richarddzh/minibox/assets/esp32s3_devkit.jpg

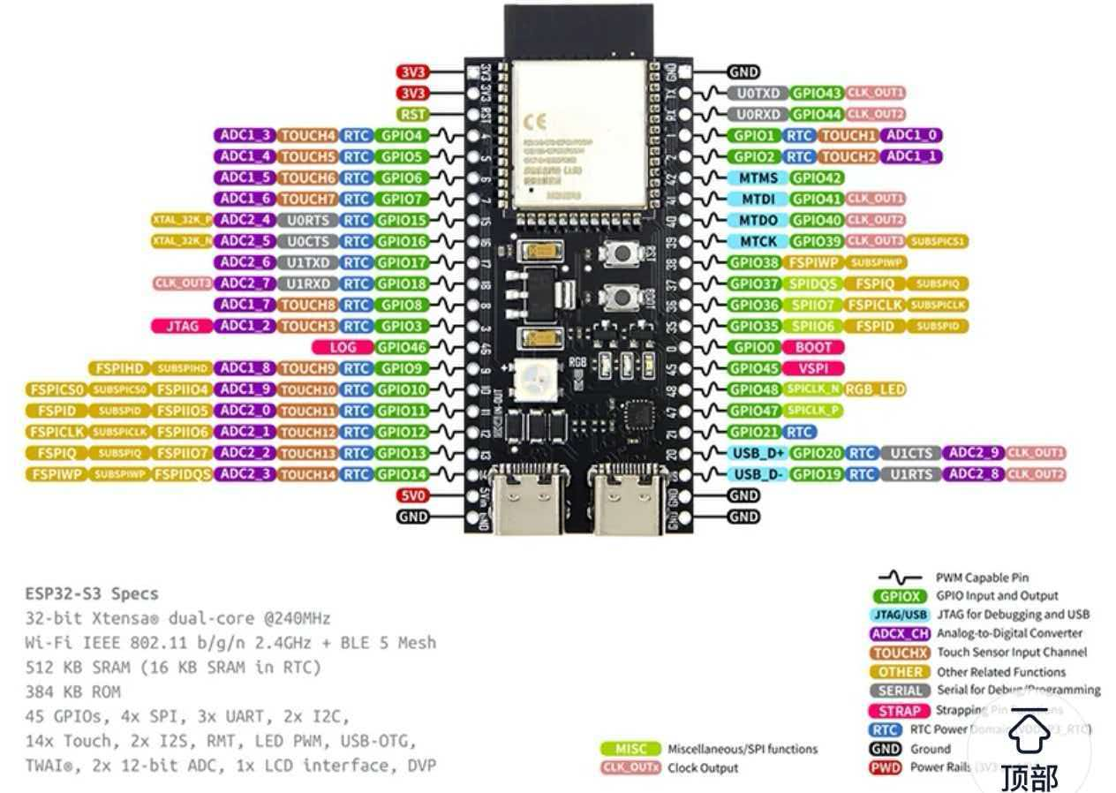
assets/esp32s3_devkit.jpg
