richarddzh/minibox/assets/keypad.jpg

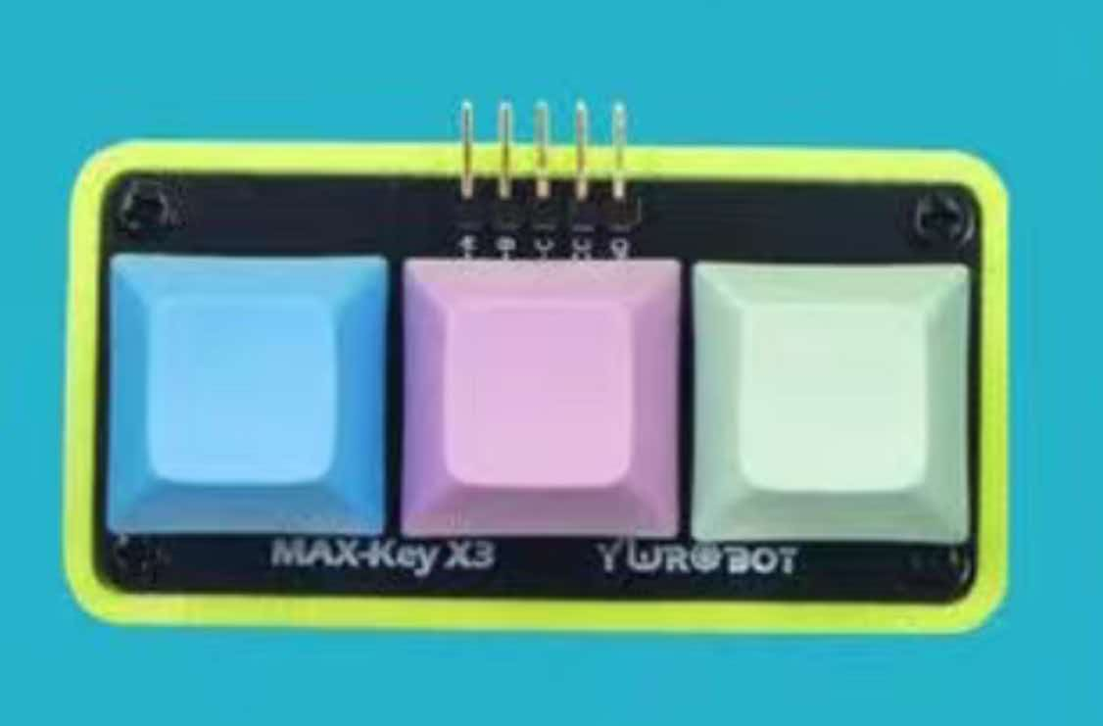
assets/keypad.jpg
