richarddzh/minibox/assets/crimp_terminal.jpg

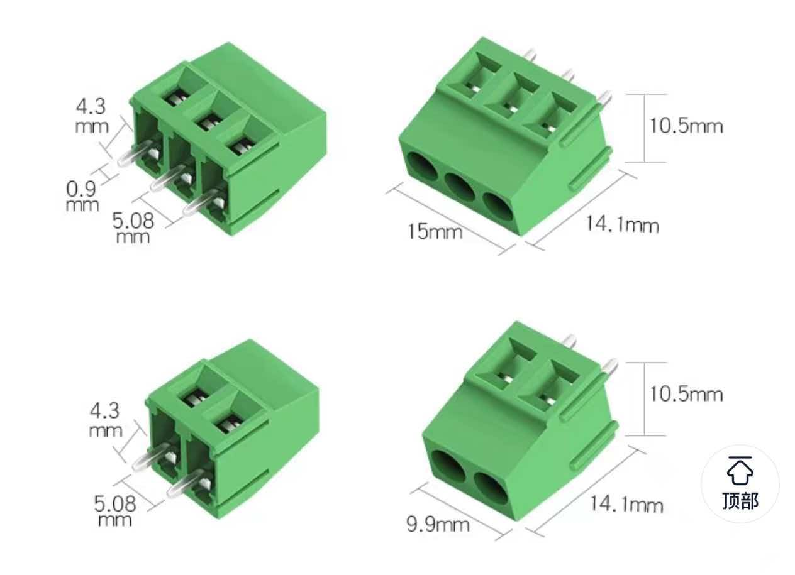
assets/crimp_terminal.jpg
