richarddzh/minibox/assets/esp32s3_devkit_01.jpg

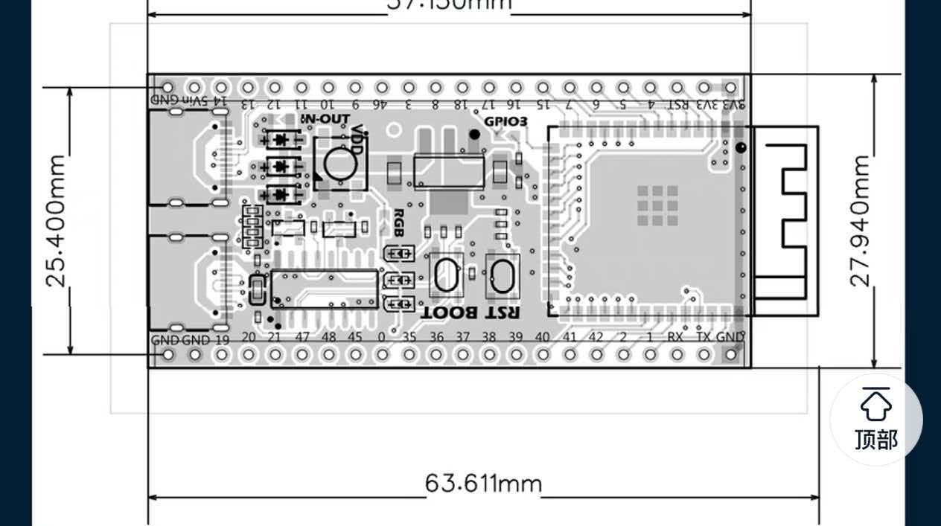
assets/esp32s3_devkit_01.jpg
