richarddzh/minibox/assets/inmp441_01.jpg

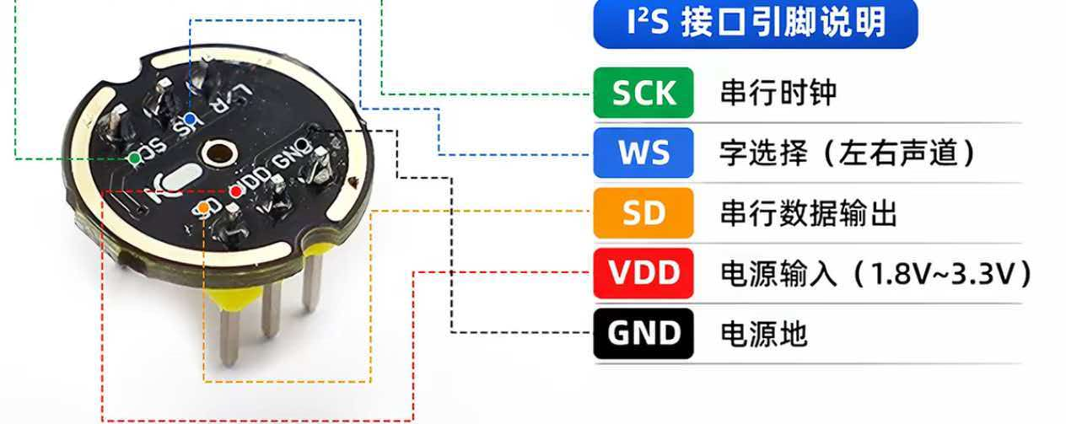
assets/inmp441_01.jpg
