richarddzh/minibox/assets/inmp441_02.jpg

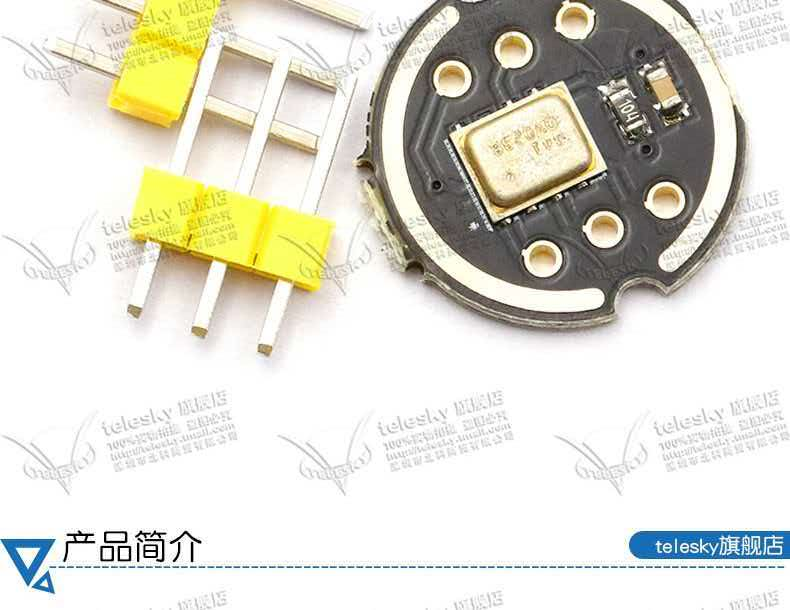
assets/inmp441_02.jpg
