richarddzh/minibox/assets/joystick.jpg

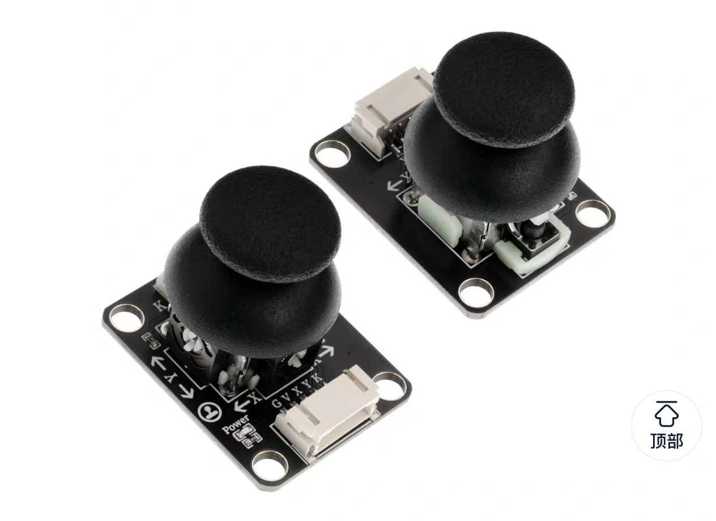
assets/joystick.jpg
