richarddzh/minibox/assets/max98357a_01.jpg

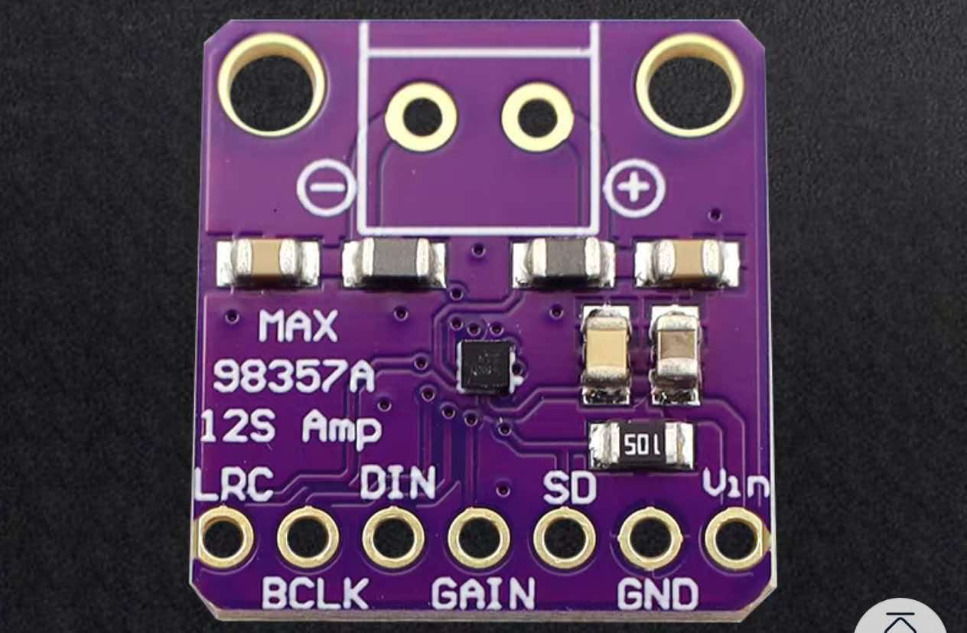
assets/max98357a_01.jpg
