richarddzh/minibox/assets/max98357a_02.jpg

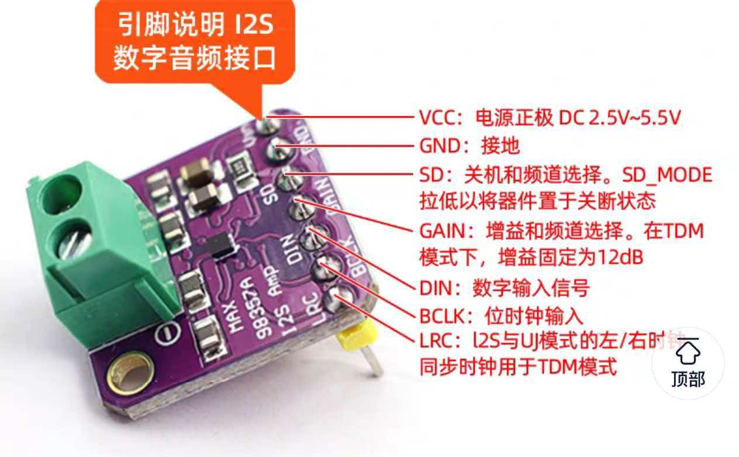
assets/max98357a_02.jpg
