richarddzh/minibox/assets/pcf8563t_rtc.jpg

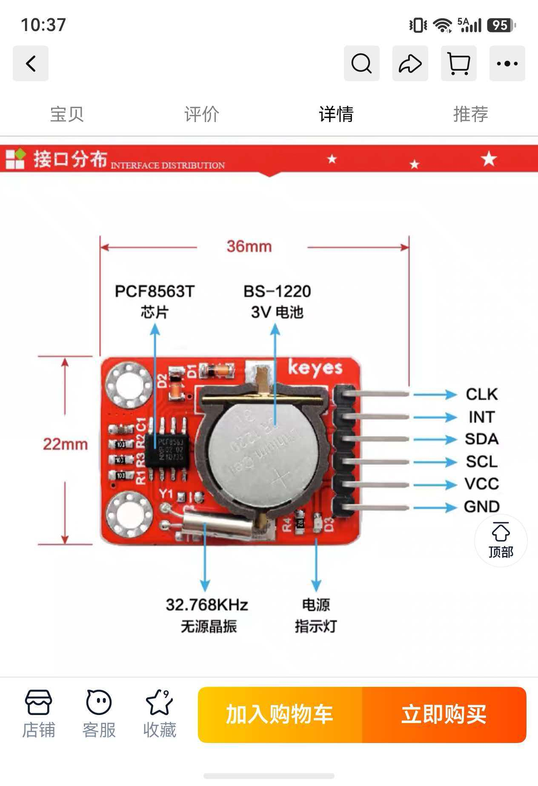
assets/pcf8563t_rtc.jpg
