richarddzh/minibox/assets/tft_spi.jpg

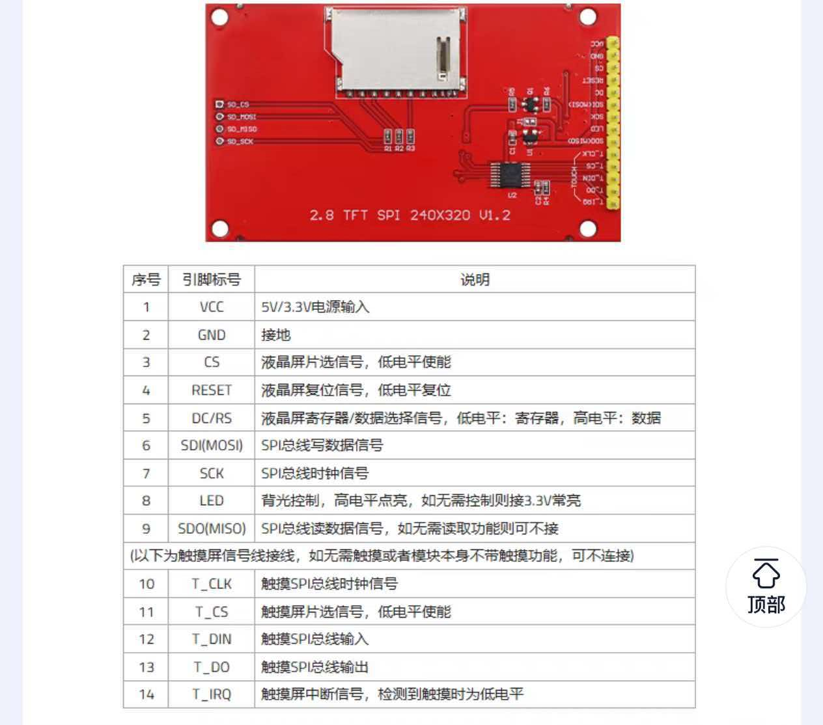
assets/tft_spi.jpg
