richarddzh/minibox/hardware_references/drawings/cpg151101d13-lcsc-pcb.png

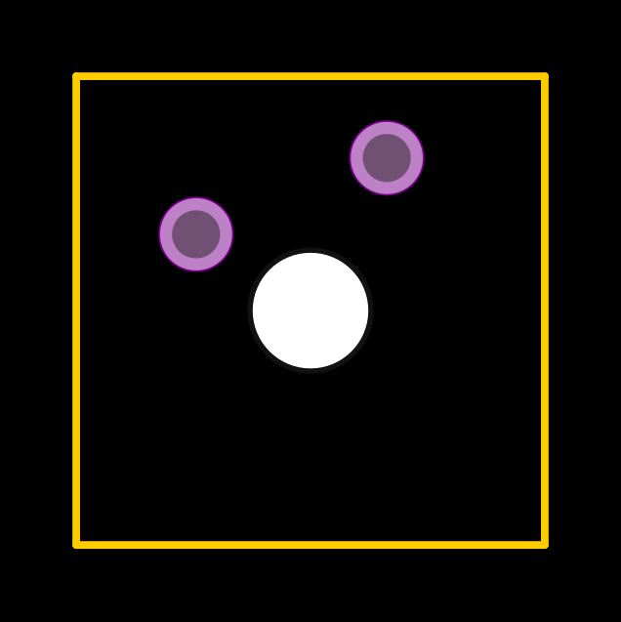
hardware_references/drawings/cpg151101d13-lcsc-pcb.png
