richarddzh/minibox/hardware_references/drawings/cpg151101d13-page-6.png

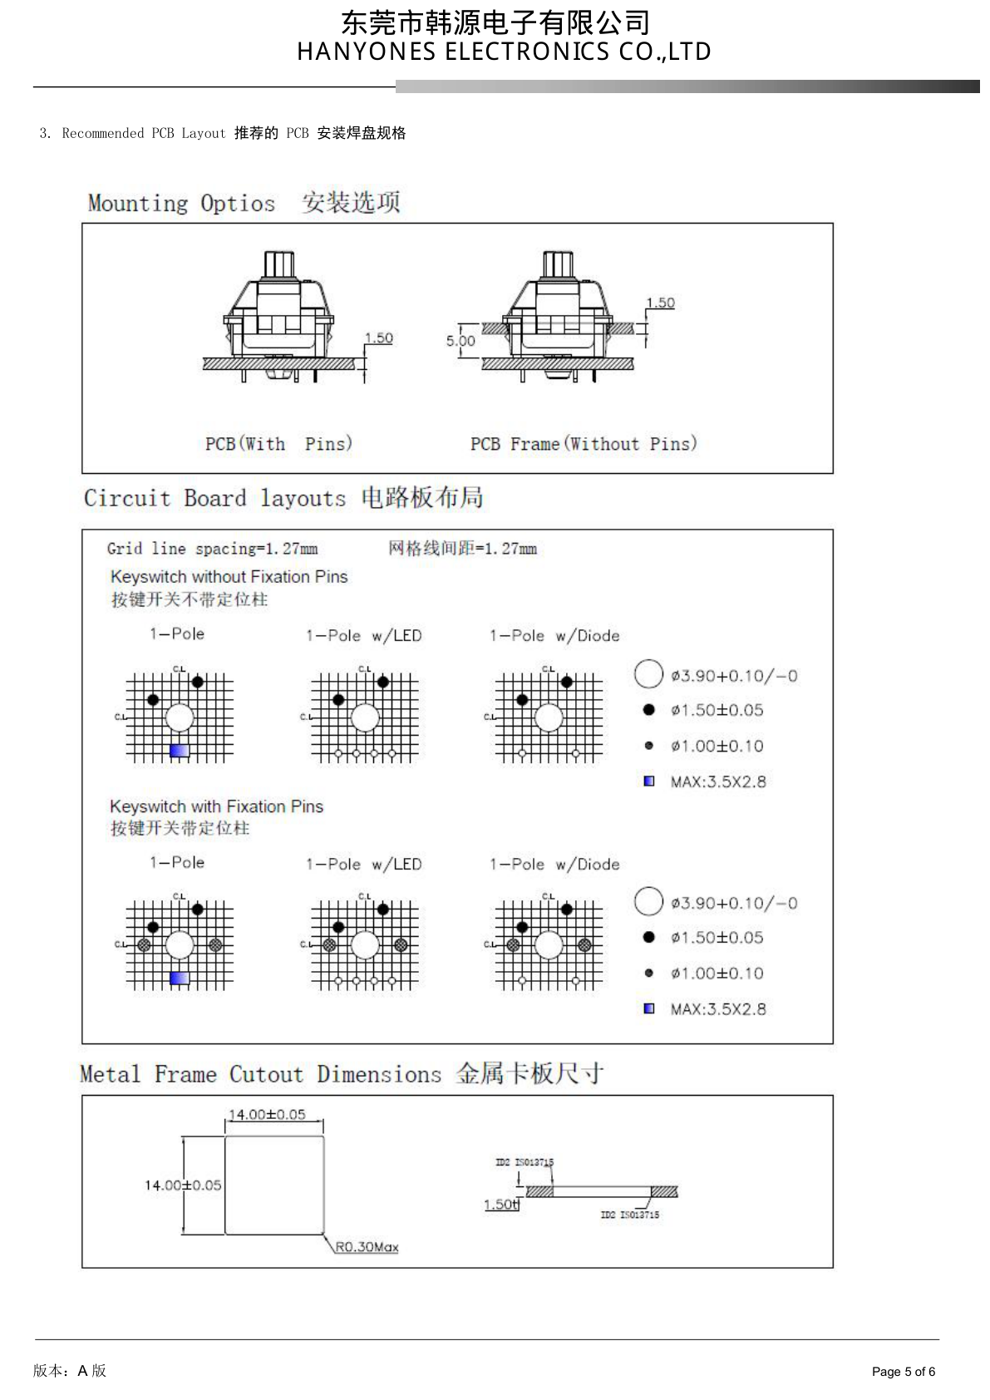
hardware_references/drawings/cpg151101d13-page-6.png
