richarddzh/minibox/hardware_references/drawings/ds3231-9.png

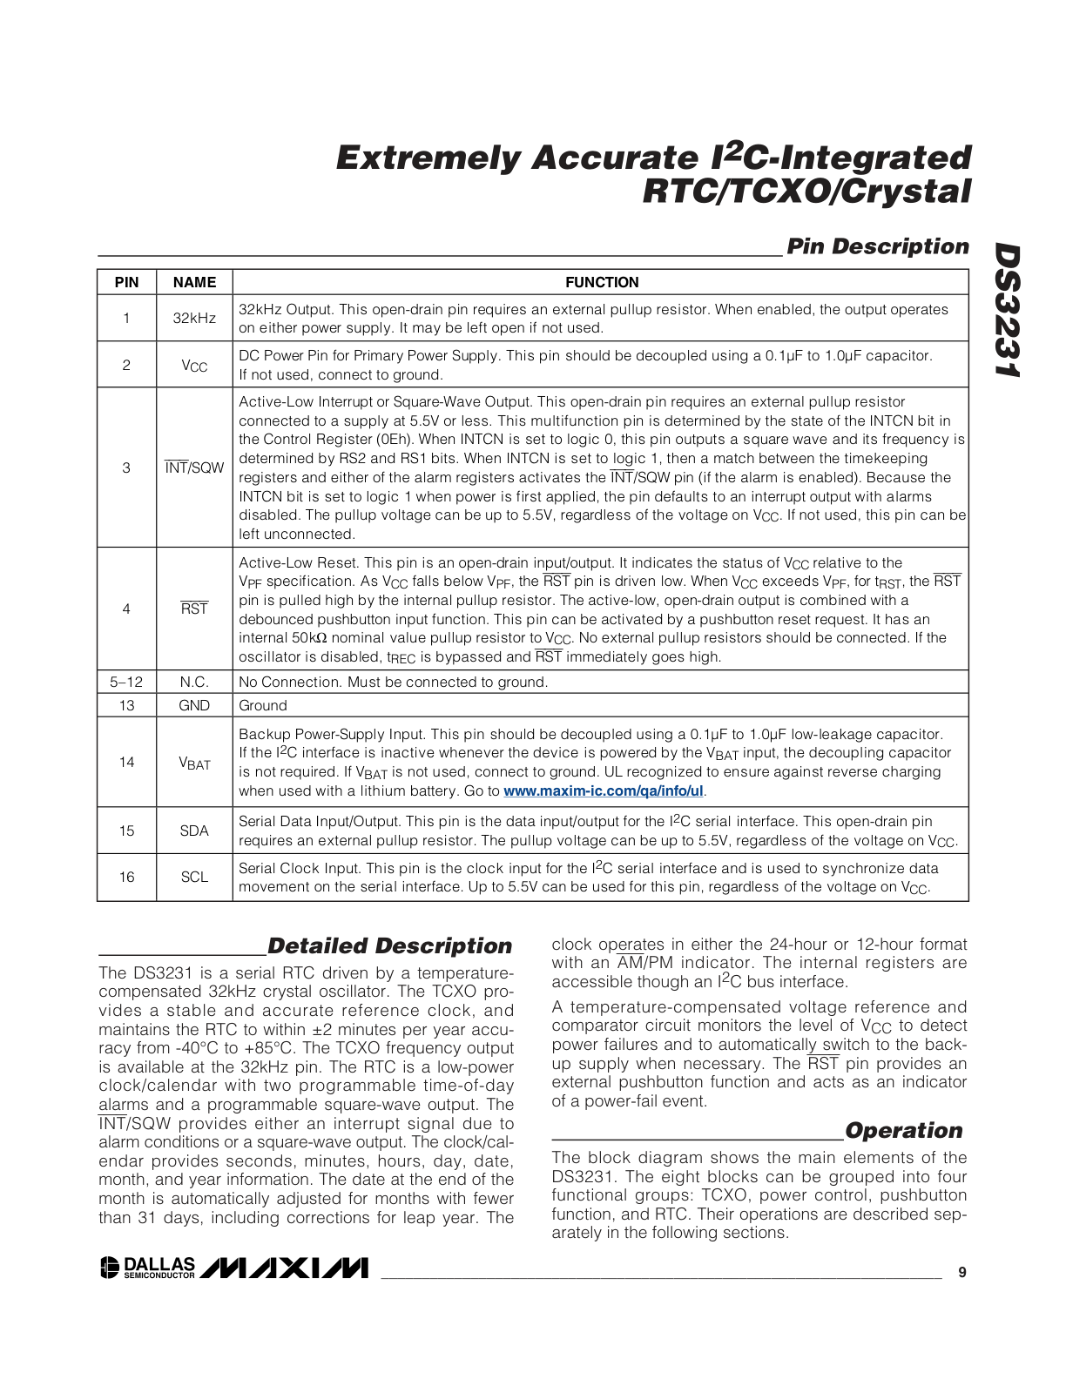
hardware_references/drawings/ds3231-9.png
