richarddzh/minibox/hardware_references/drawings/ds3231-20.png

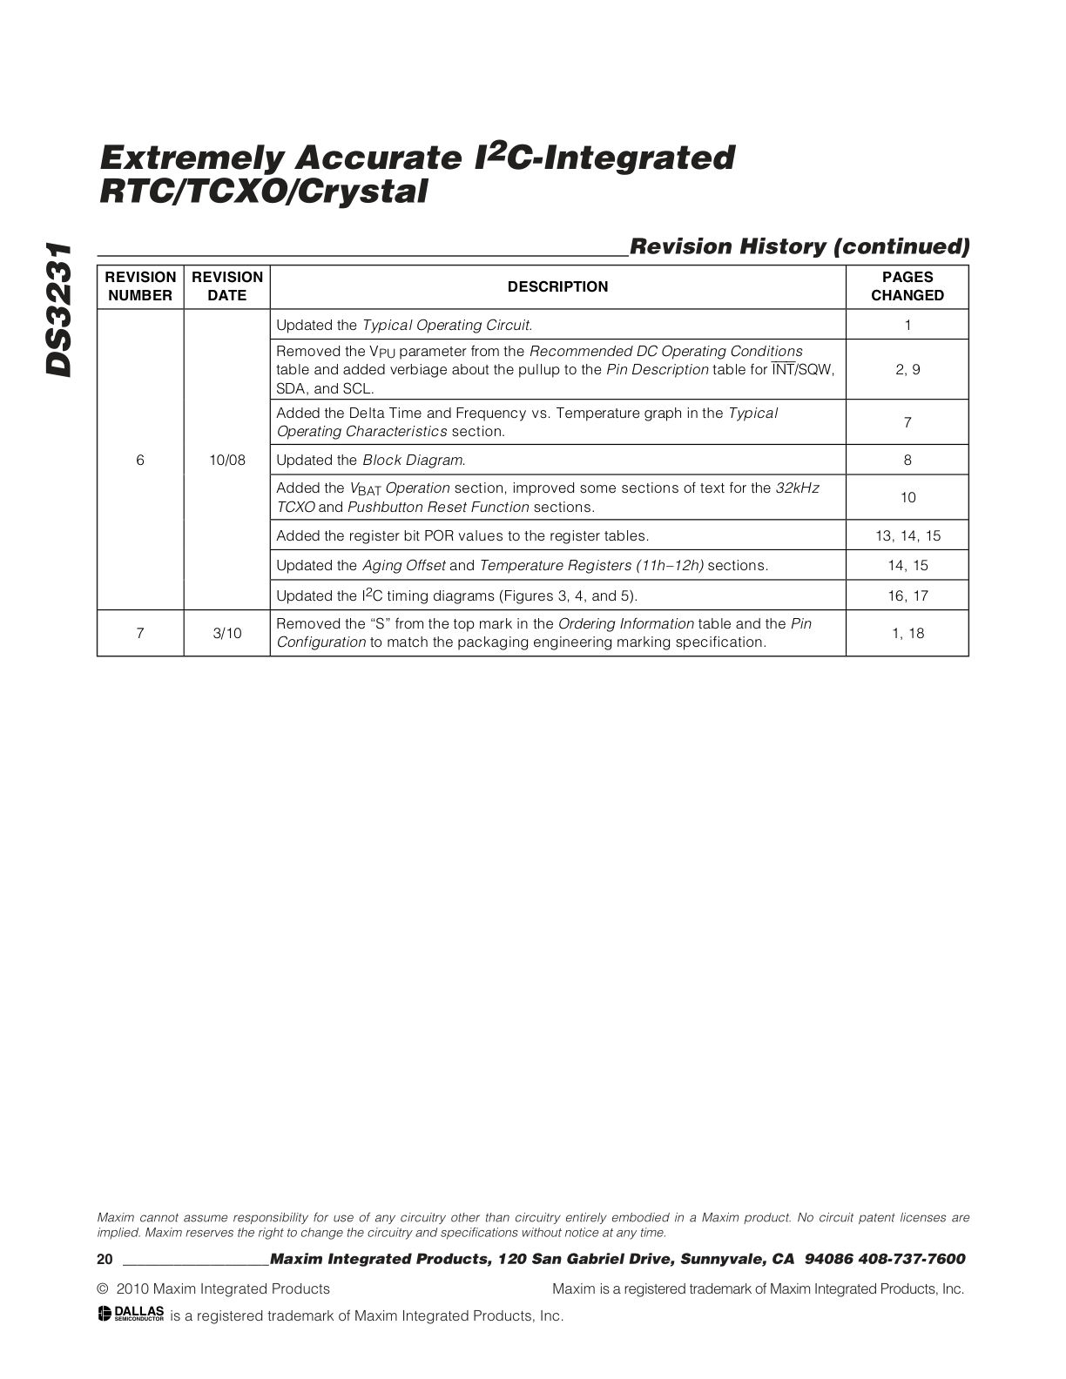
hardware_references/drawings/ds3231-20.png
