richarddzh/minibox/hardware_references/drawings/inmp441-page-8.png

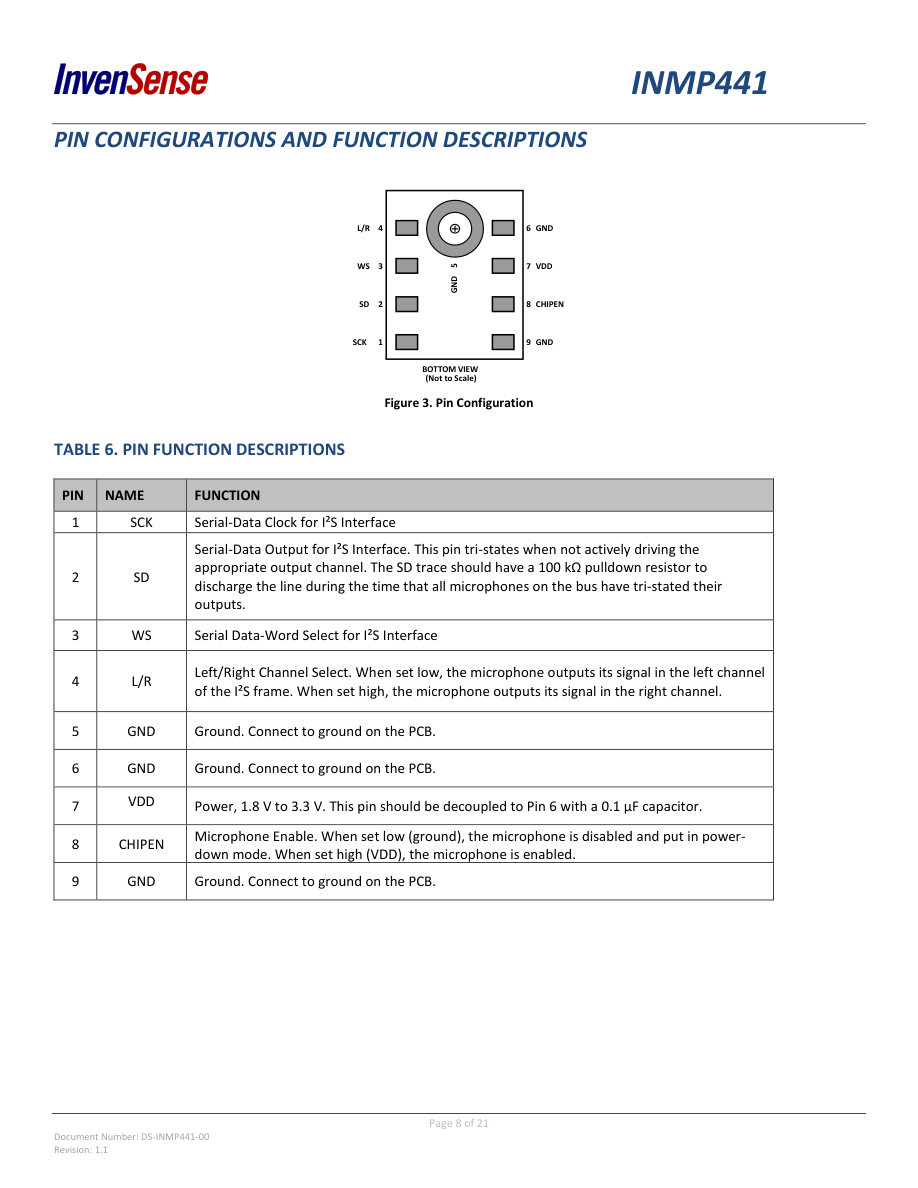
hardware_references/drawings/inmp441-page-8.png
