richarddzh/minibox/hardware_references/drawings/inmp441-page-17.png

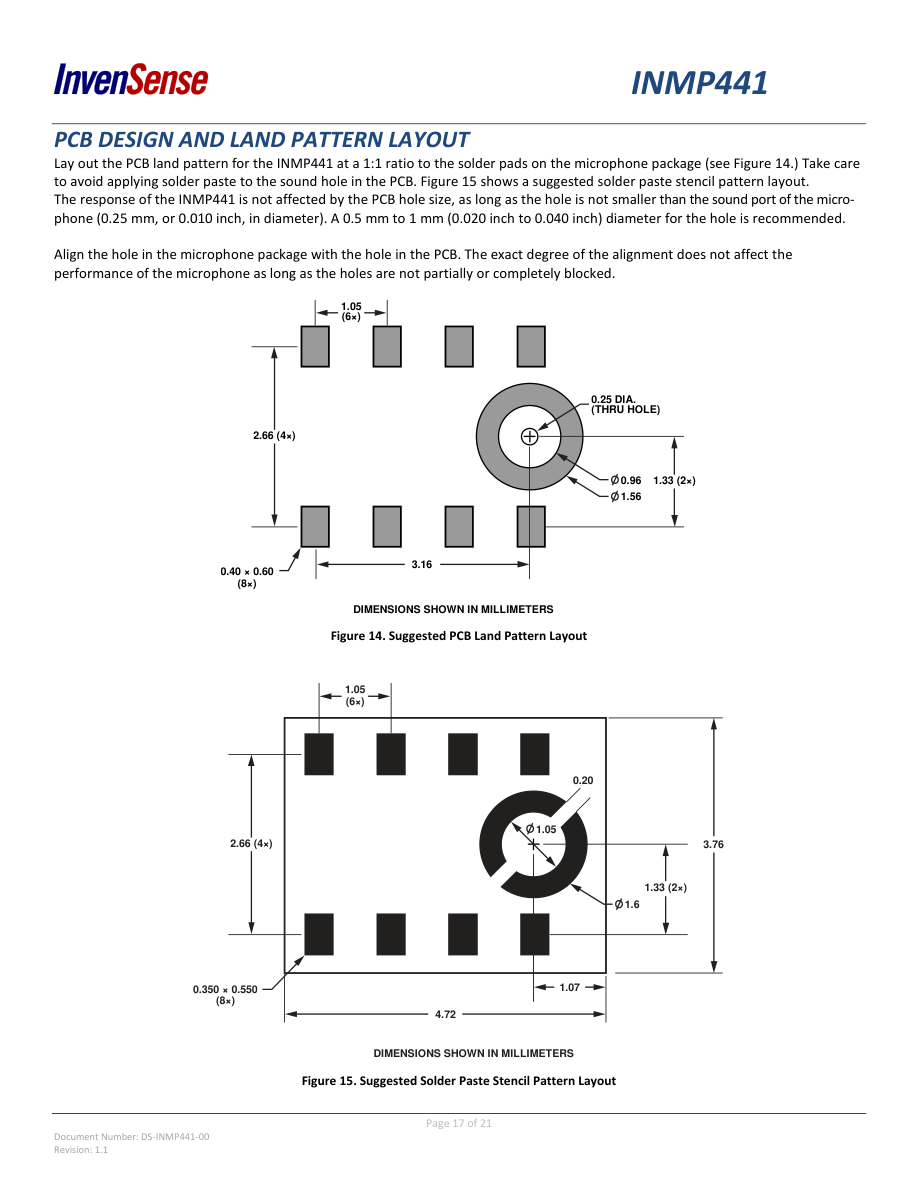
hardware_references/drawings/inmp441-page-17.png
