richarddzh/minibox/hardware_references/drawings/myoung-bs-12-b3aa003-1.png

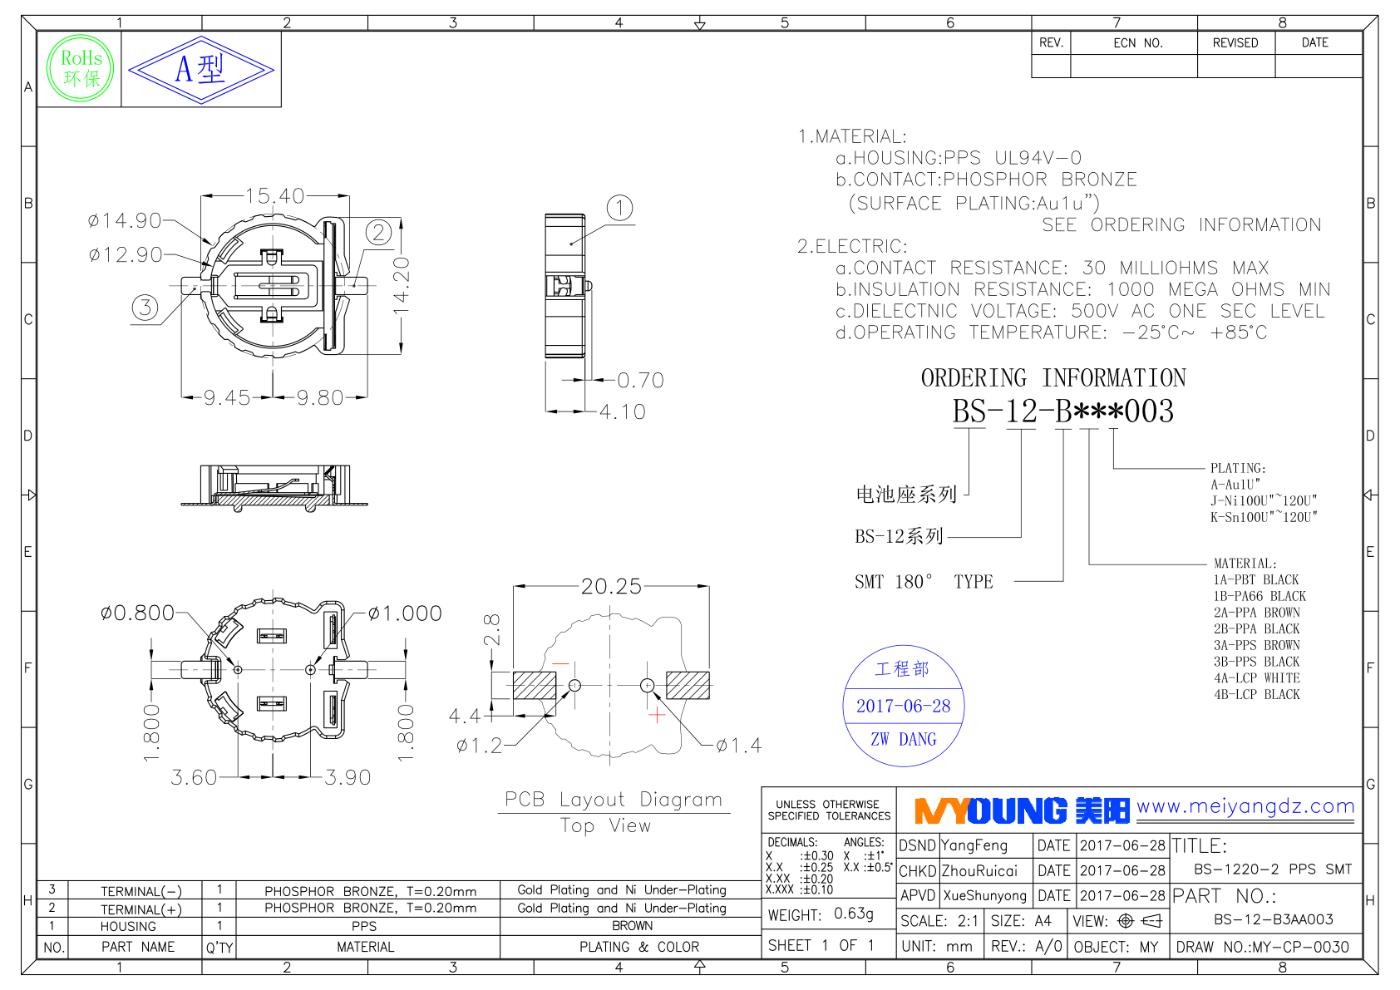
hardware_references/drawings/myoung-bs-12-b3aa003-1.png
