richarddzh/minibox/hardware_references/drawings/requested-layout-20261009.png

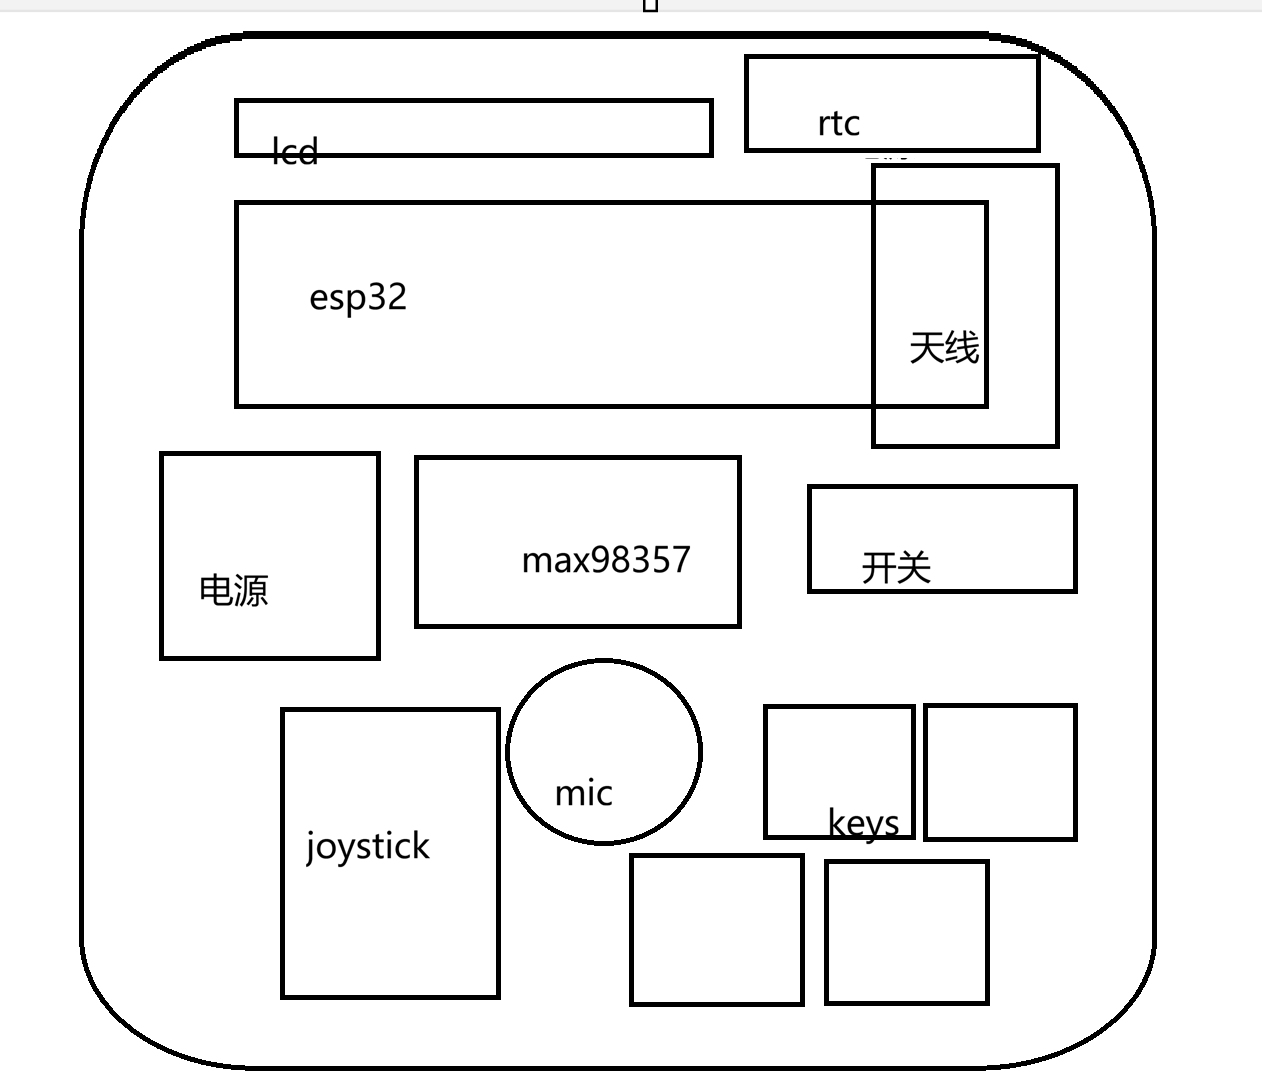
hardware_references/drawings/requested-layout-20261009.png
