richarddzh/minibox/hardware_references/drawings/requested-layout.png

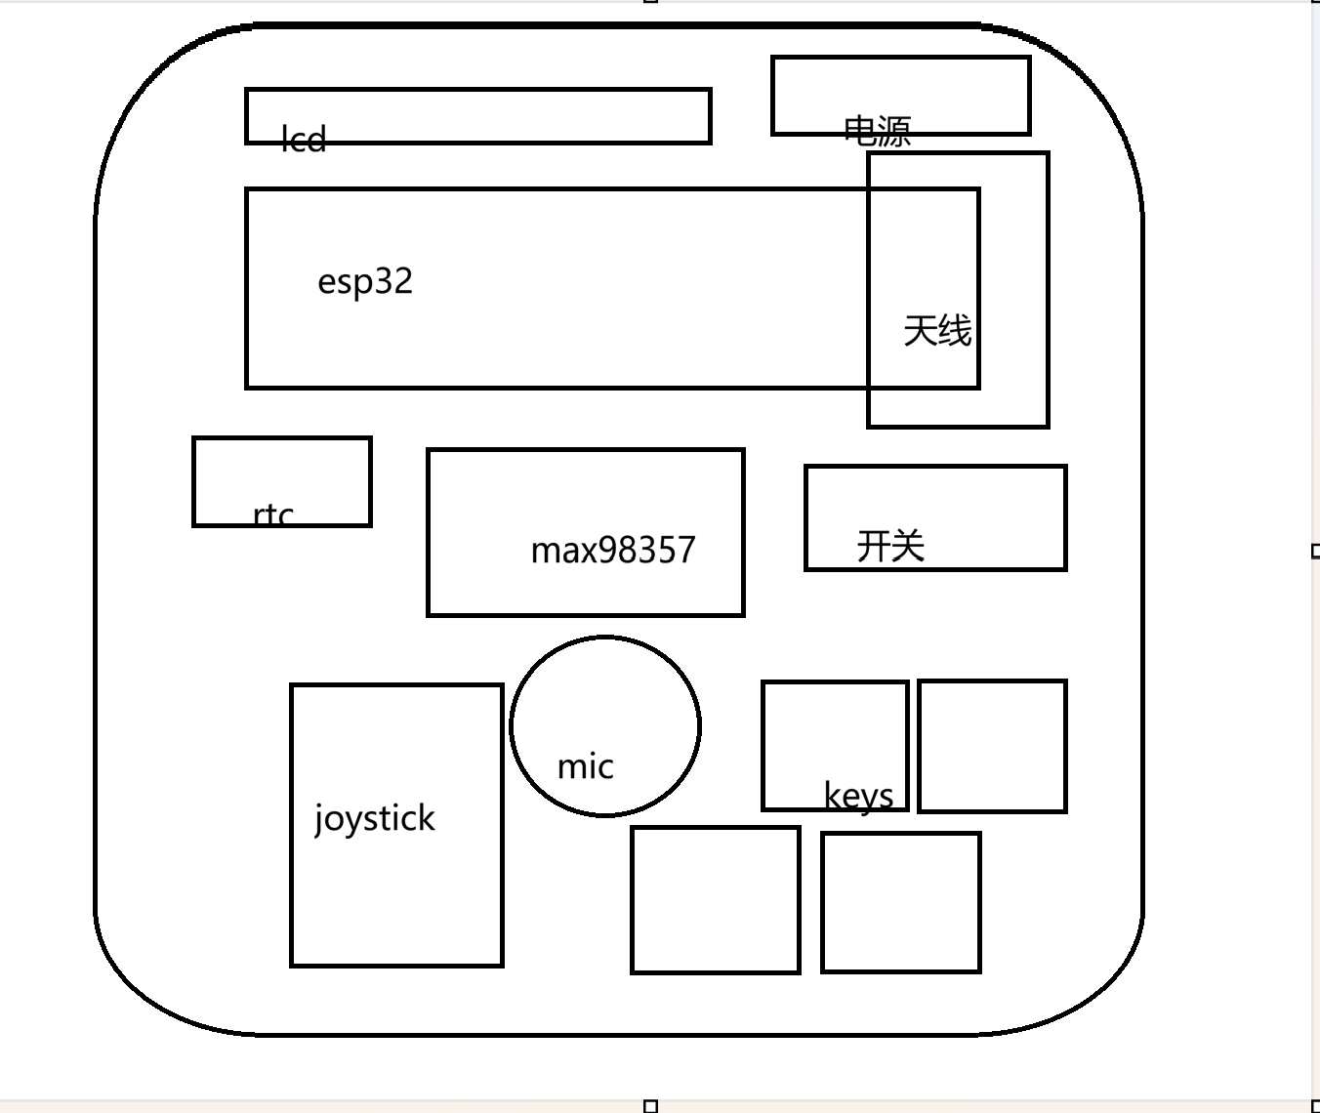
hardware_references/drawings/requested-layout.png
