richarddzh/minibox/hardware_references/drawings/rkjxv-2.png

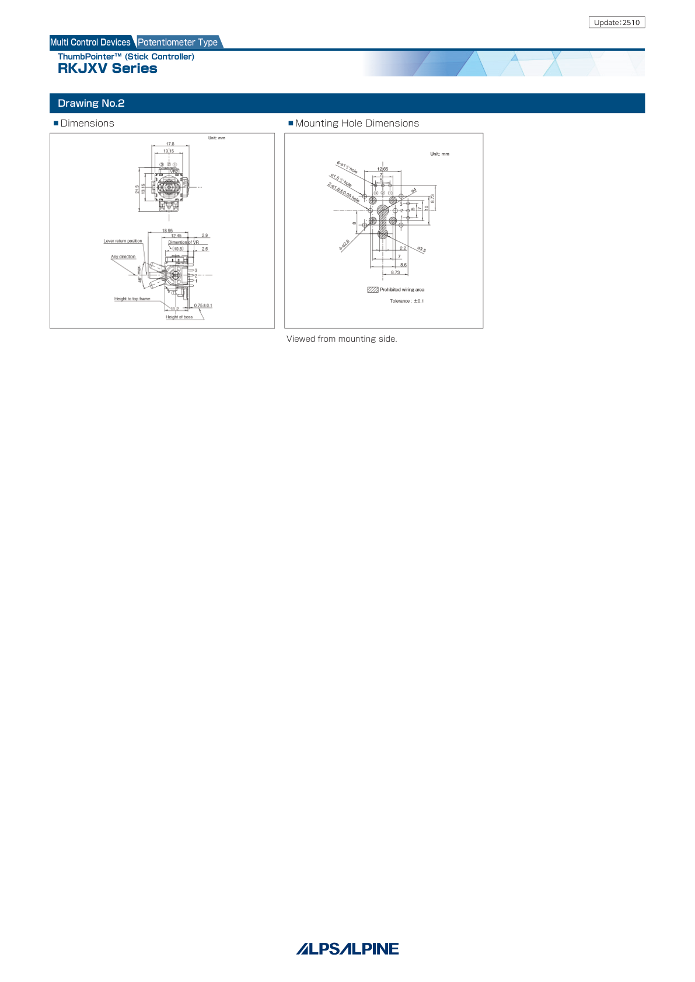
hardware_references/drawings/rkjxv-2.png
