richarddzh/minibox/hardware_references/drawings/sn74lvc1g11-pins-3.png

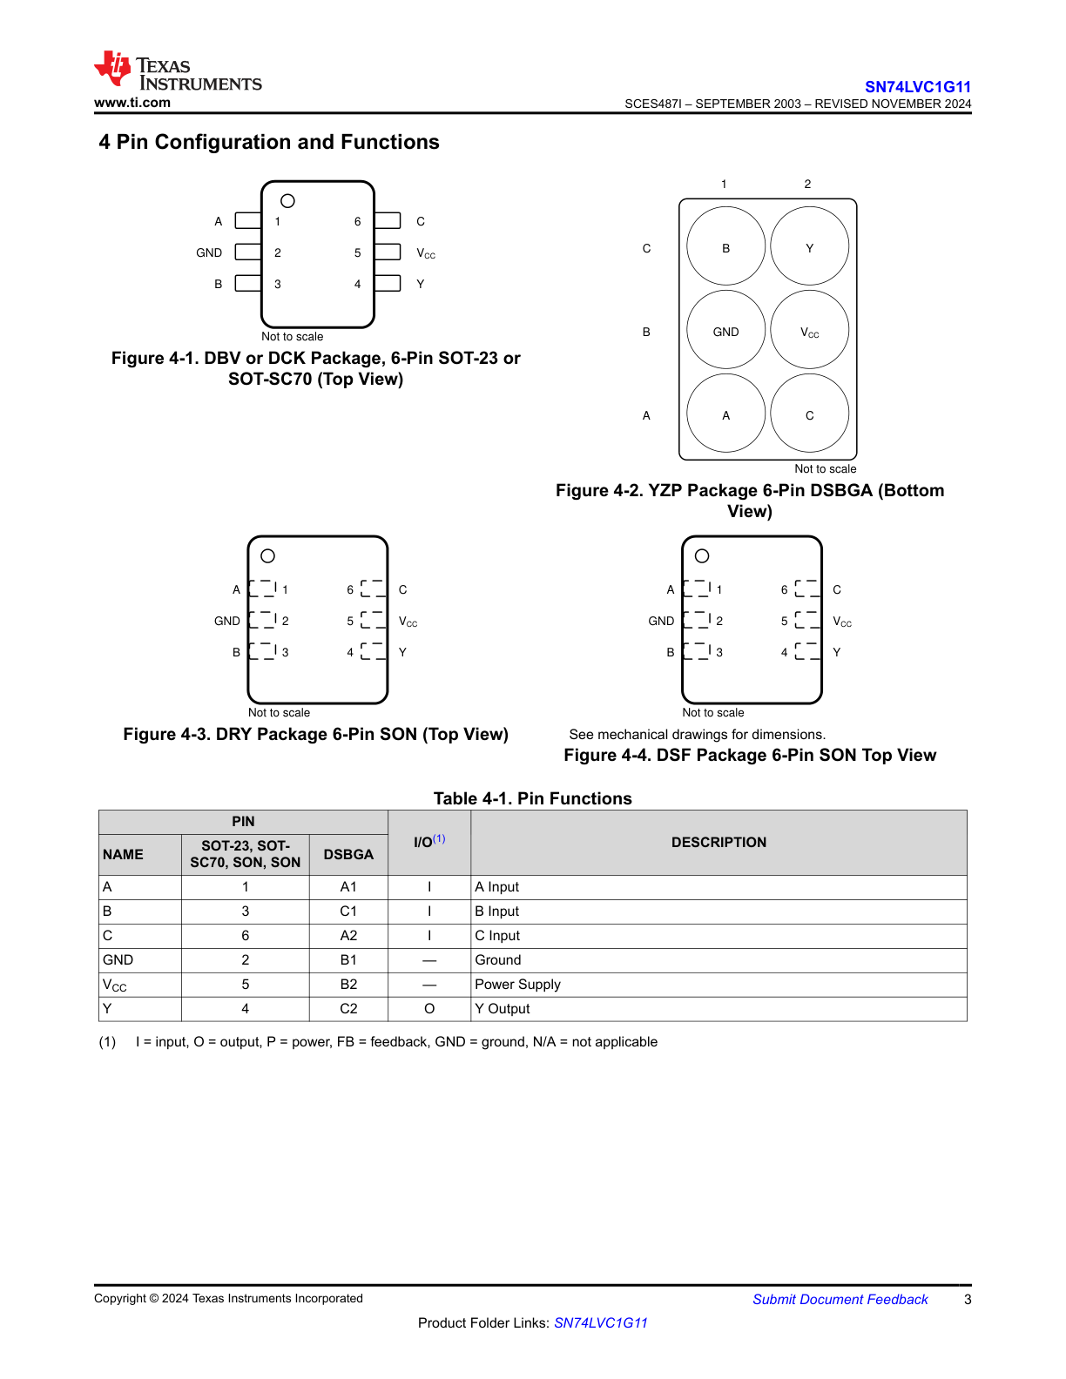
hardware_references/drawings/sn74lvc1g11-pins-3.png
