richarddzh/minibox/hardware_references/drawings/thb001p-1.png

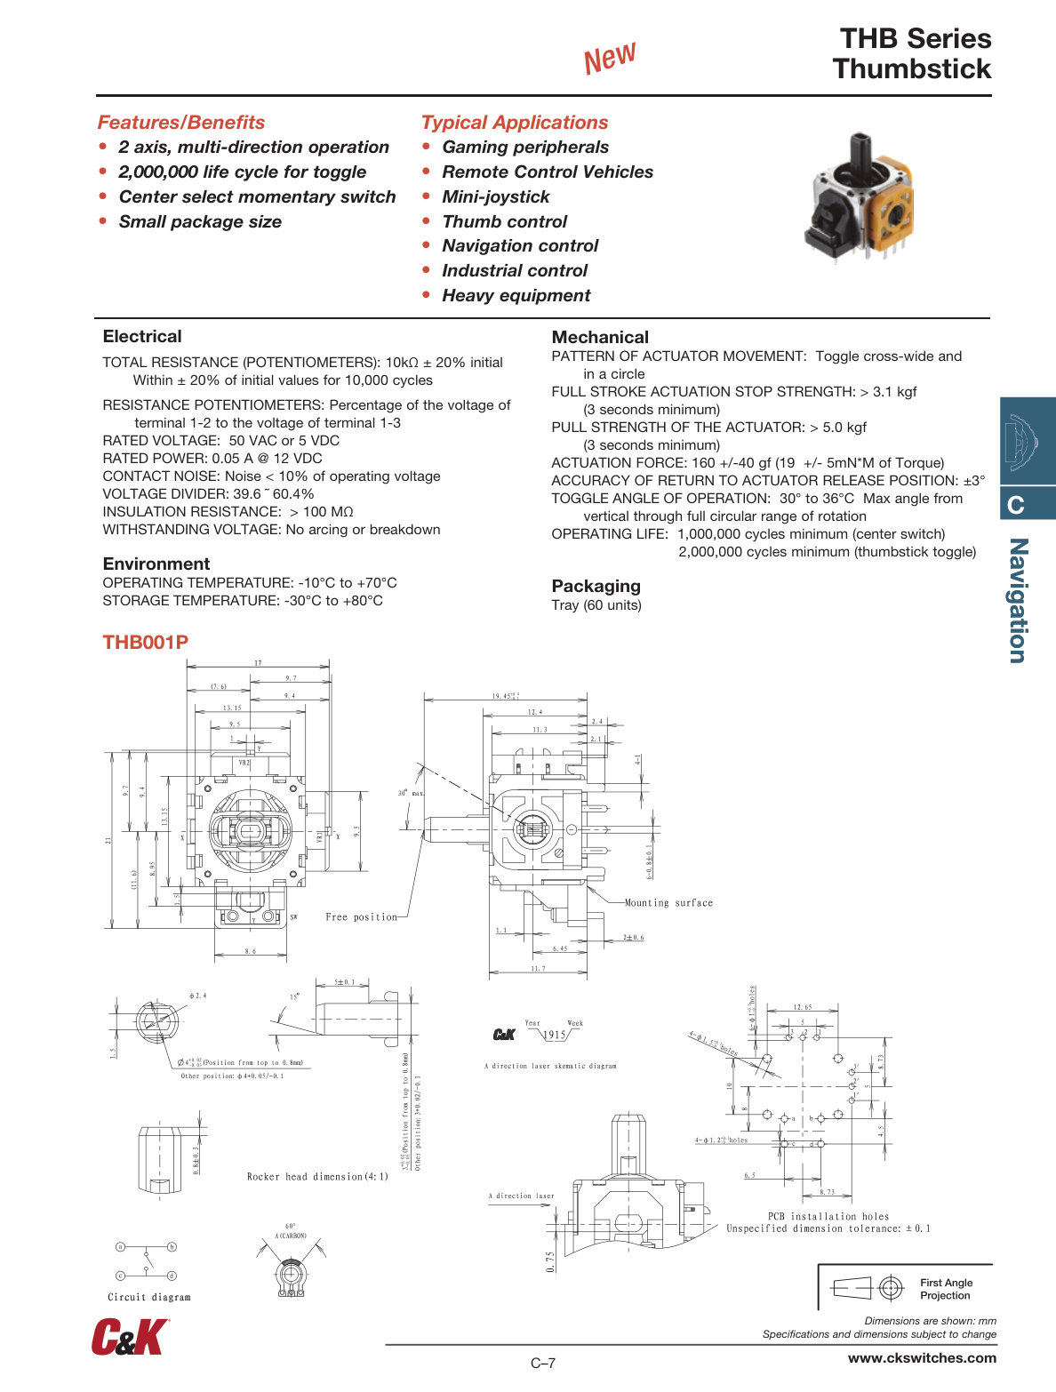
hardware_references/drawings/thb001p-1.png
