richarddzh/minibox/hardware_references/drawings/tlv431-pins-3.png

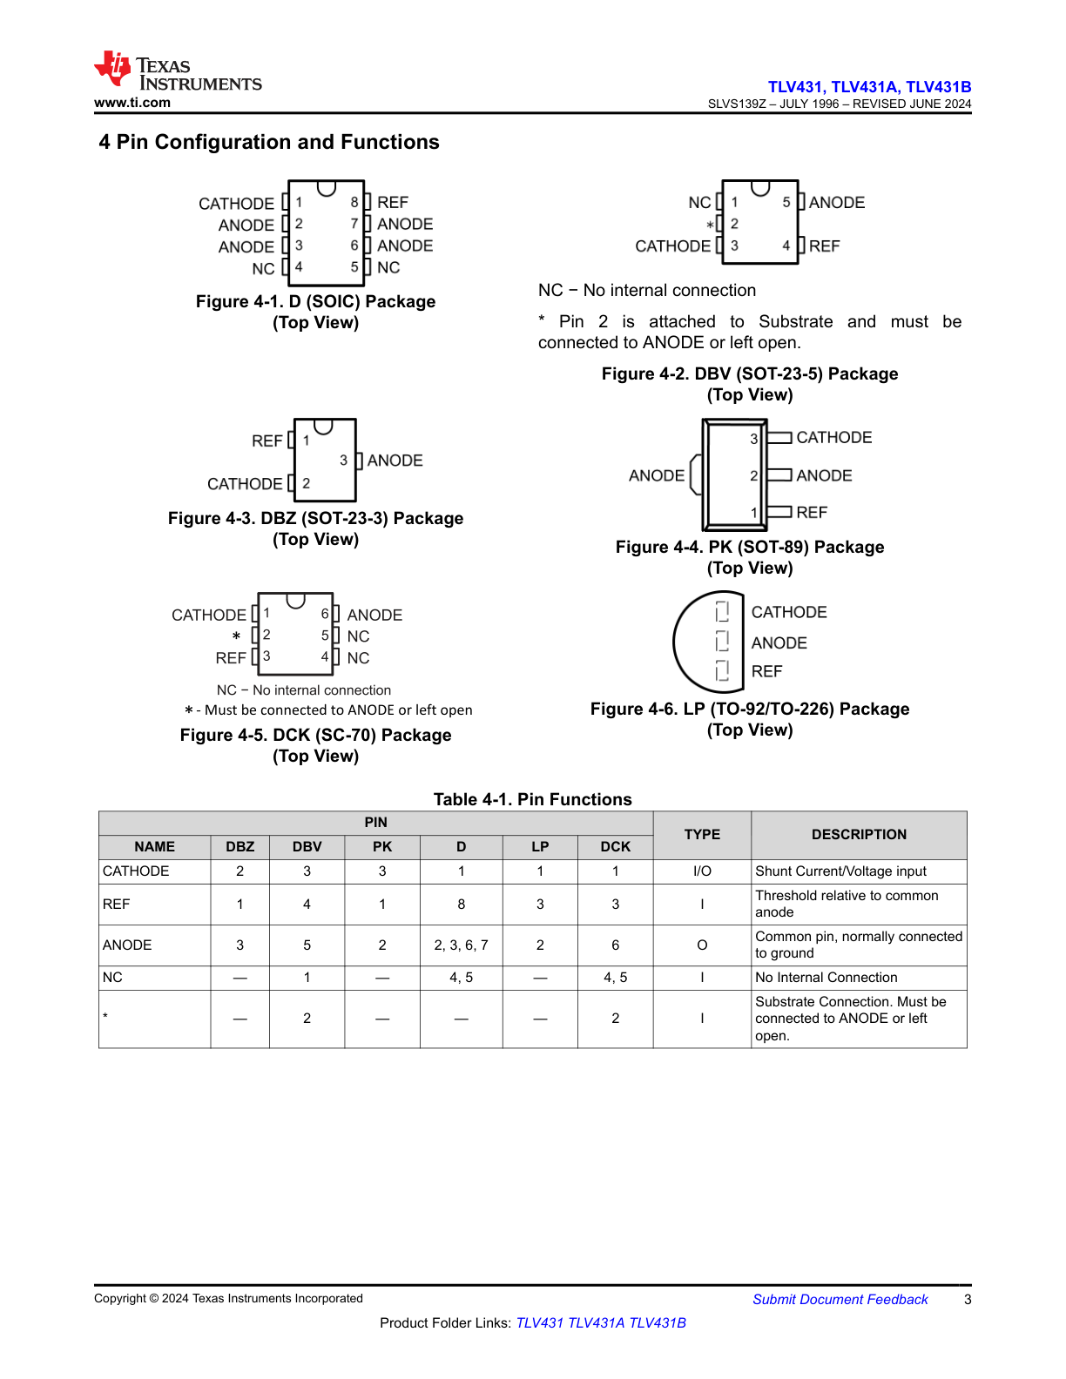
hardware_references/drawings/tlv431-pins-3.png
