richarddzh/minibox/hardware_references/drawings/tlv7034-pins-2.png

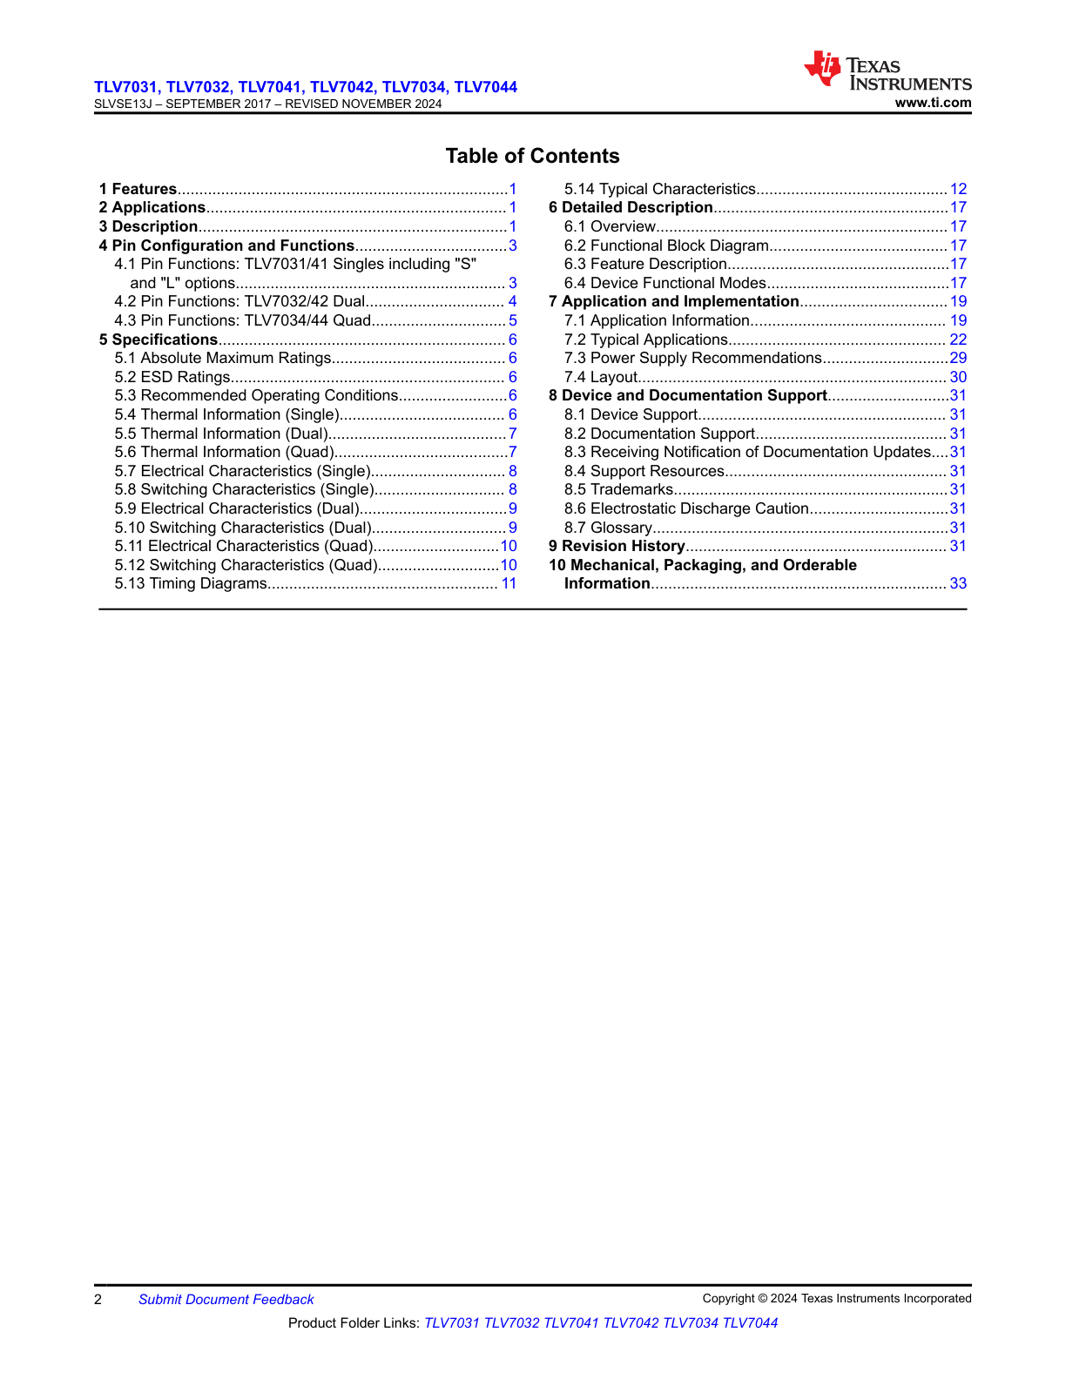
hardware_references/drawings/tlv7034-pins-2.png
