richarddzh/minibox/hardware_references/drawings/tlv7034-pins-3.png

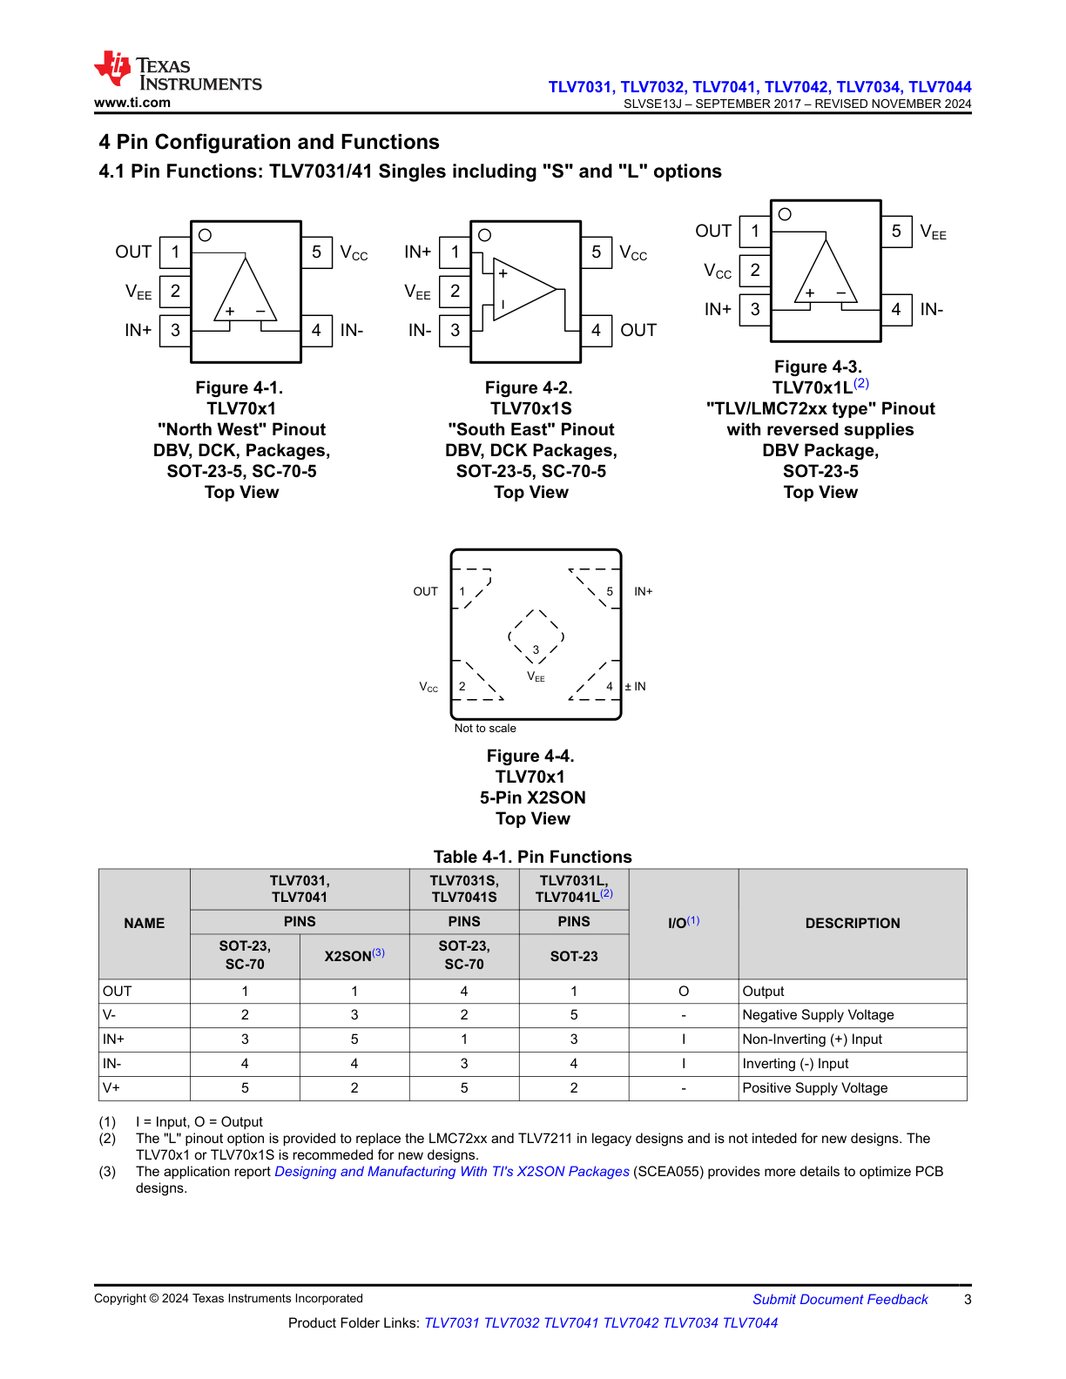
hardware_references/drawings/tlv7034-pins-3.png
