richarddzh/minibox/hardware_references/drawings/tlv7034-pins-4.png

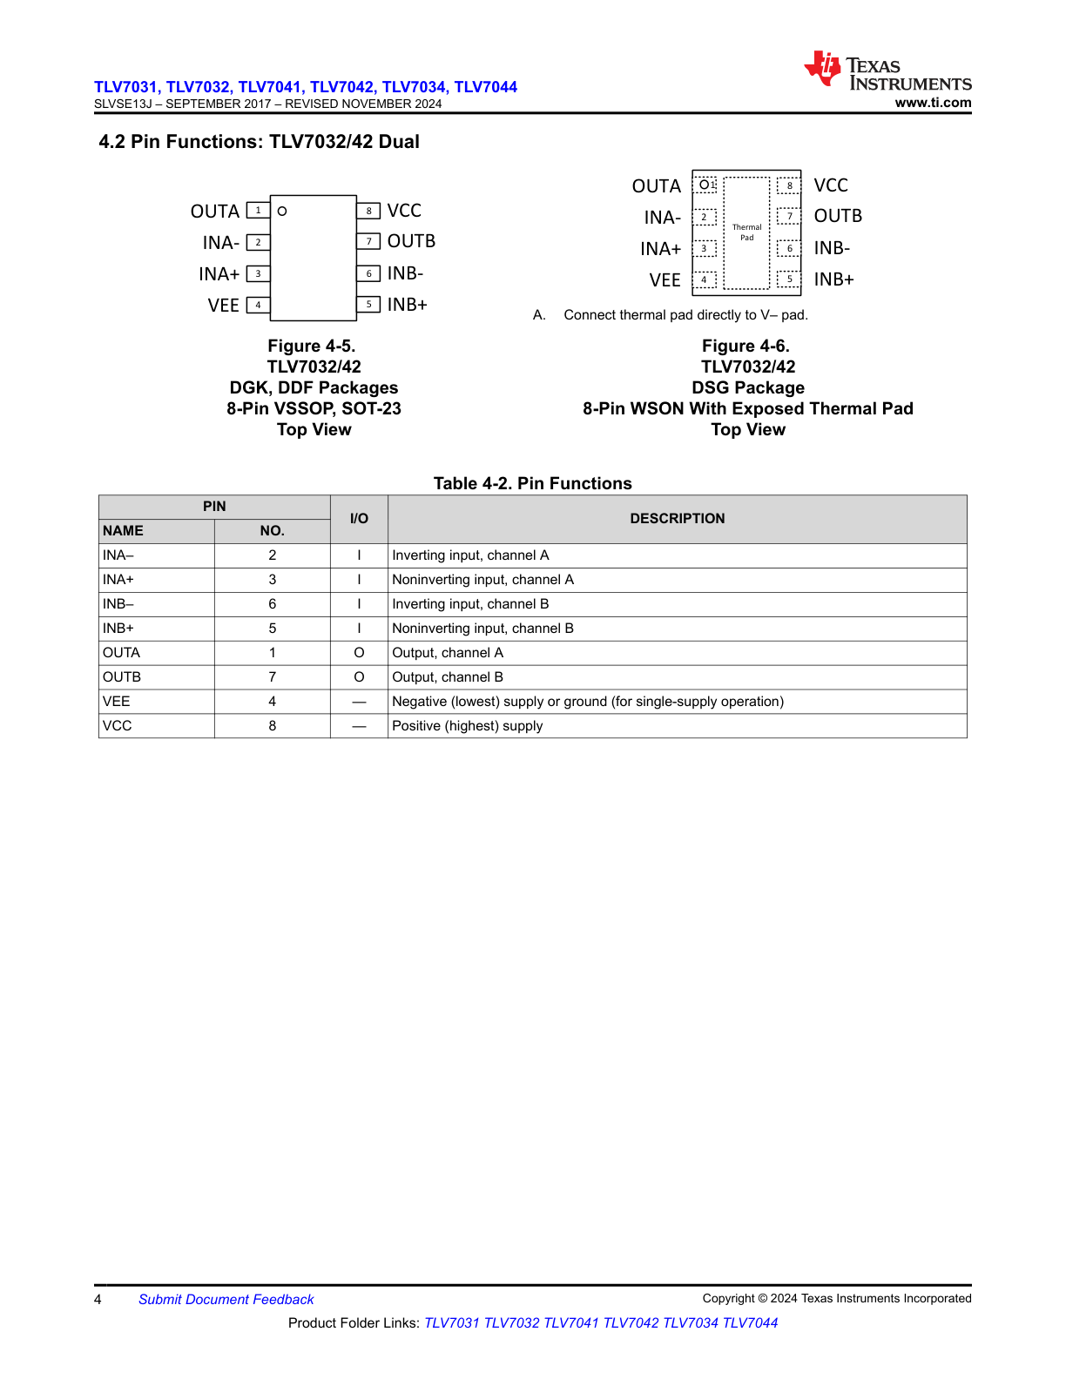
hardware_references/drawings/tlv7034-pins-4.png
