richarddzh/minibox/hardware_references/drawings/tlv7034-pins-5.png

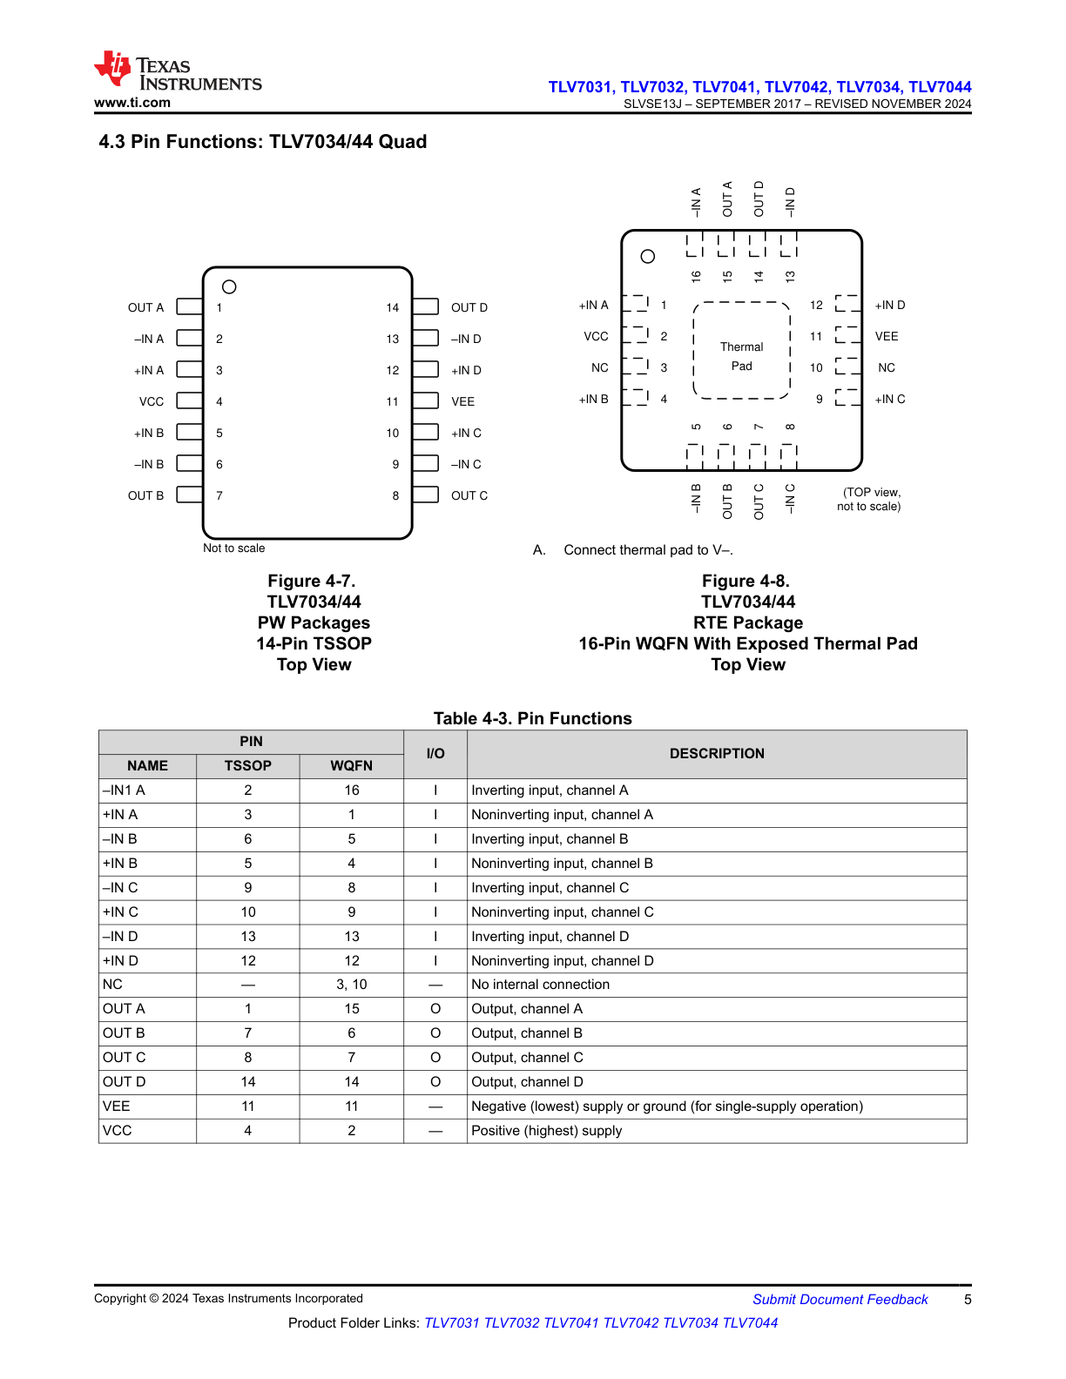
hardware_references/drawings/tlv7034-pins-5.png
