richarddzh/minibox/hardware_references/drawings/tps25947-package-72.png

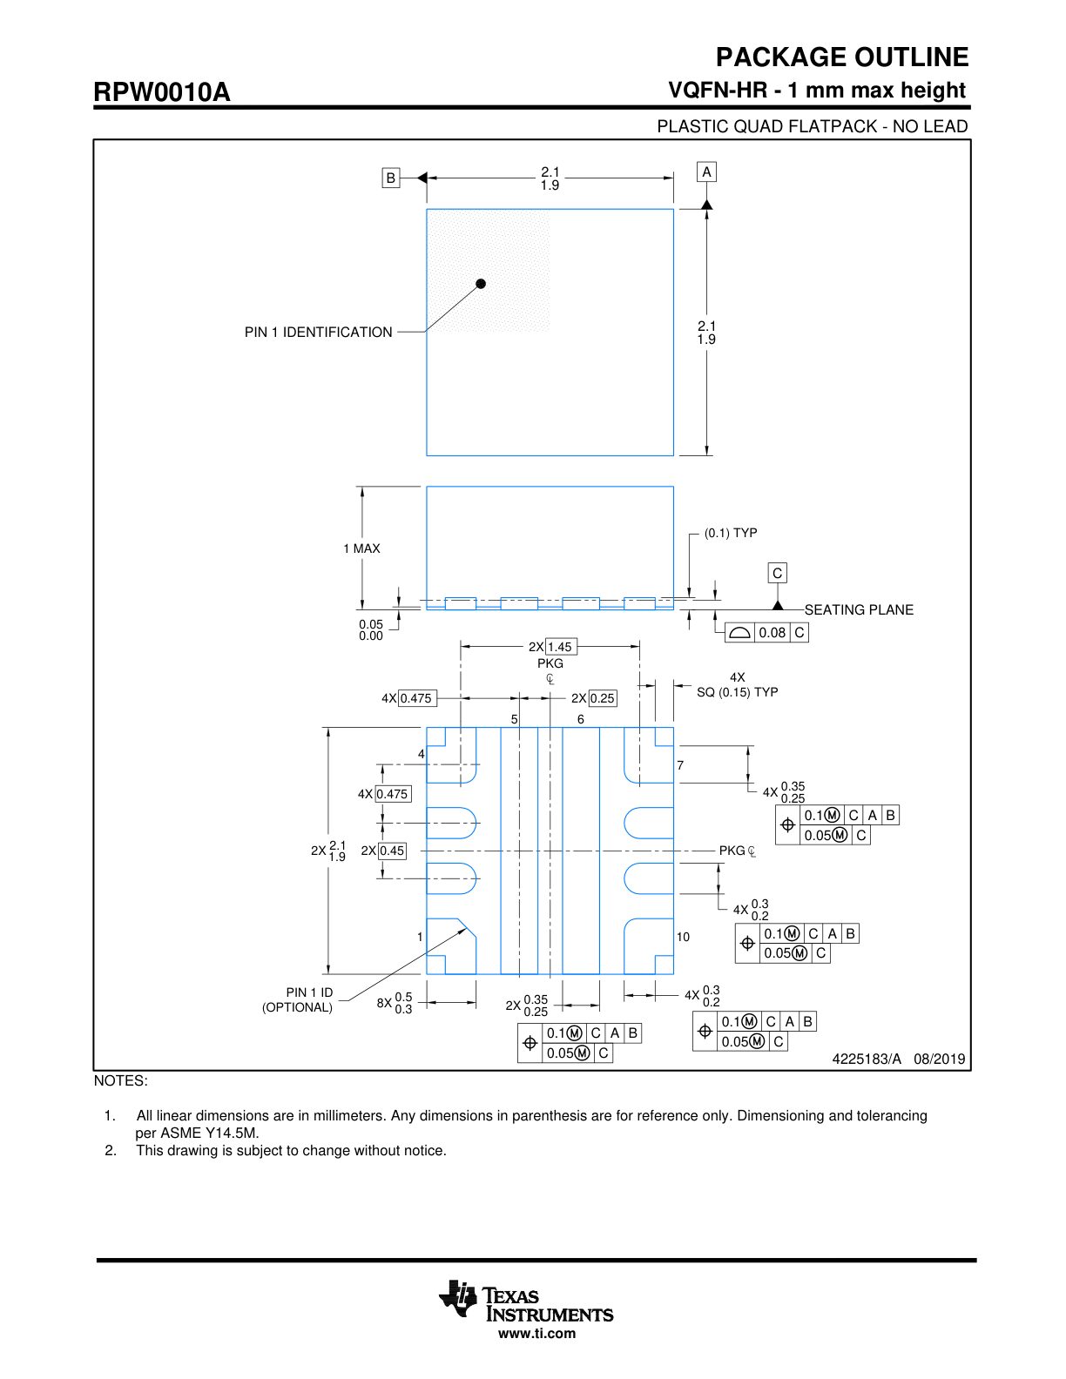
hardware_references/drawings/tps25947-package-72.png
