richarddzh/minibox/hardware_references/drawings/yv13s-l7.85-b10ka-60-0-dl01-page-2.png

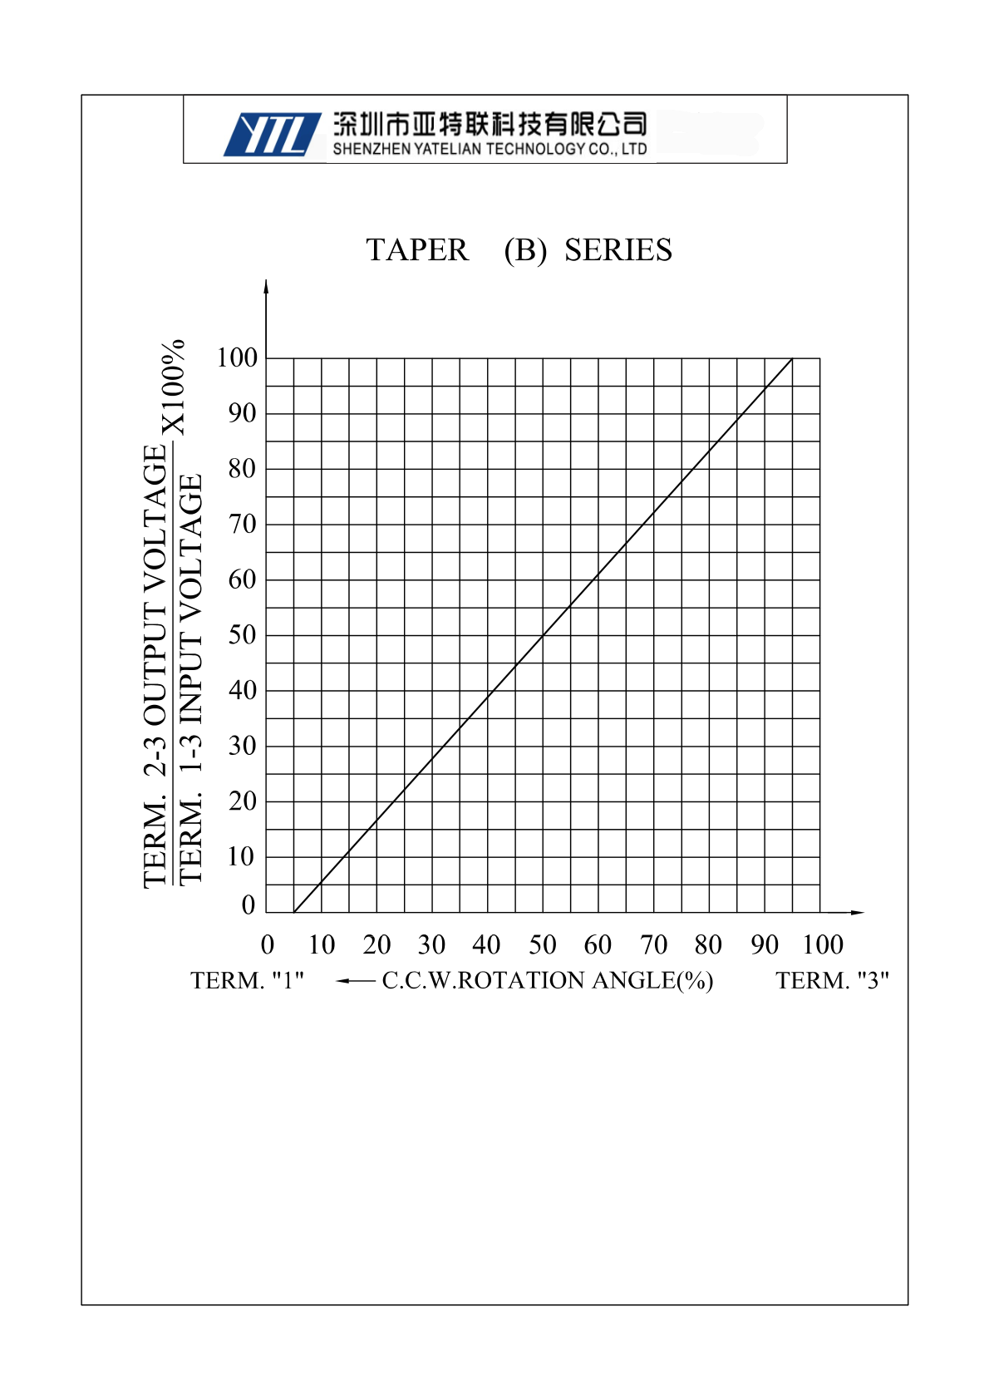
hardware_references/drawings/yv13s-l7.85-b10ka-60-0-dl01-page-2.png
