richarddzh/minibox/hardware_references/drawings/yv13s-lcsc-sch.png

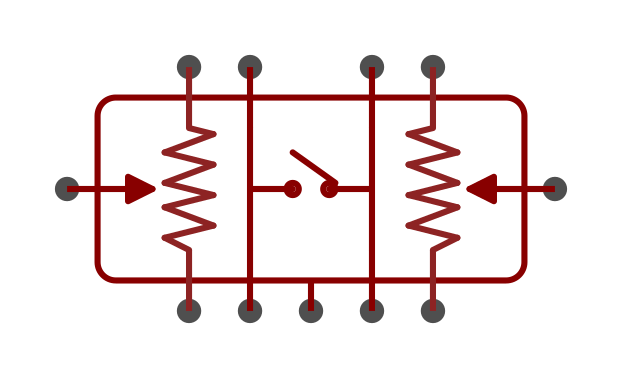
hardware_references/drawings/yv13s-lcsc-sch.png
