richarddzh/minibox/kicad/renders/minibox-carrier-back-legend.png

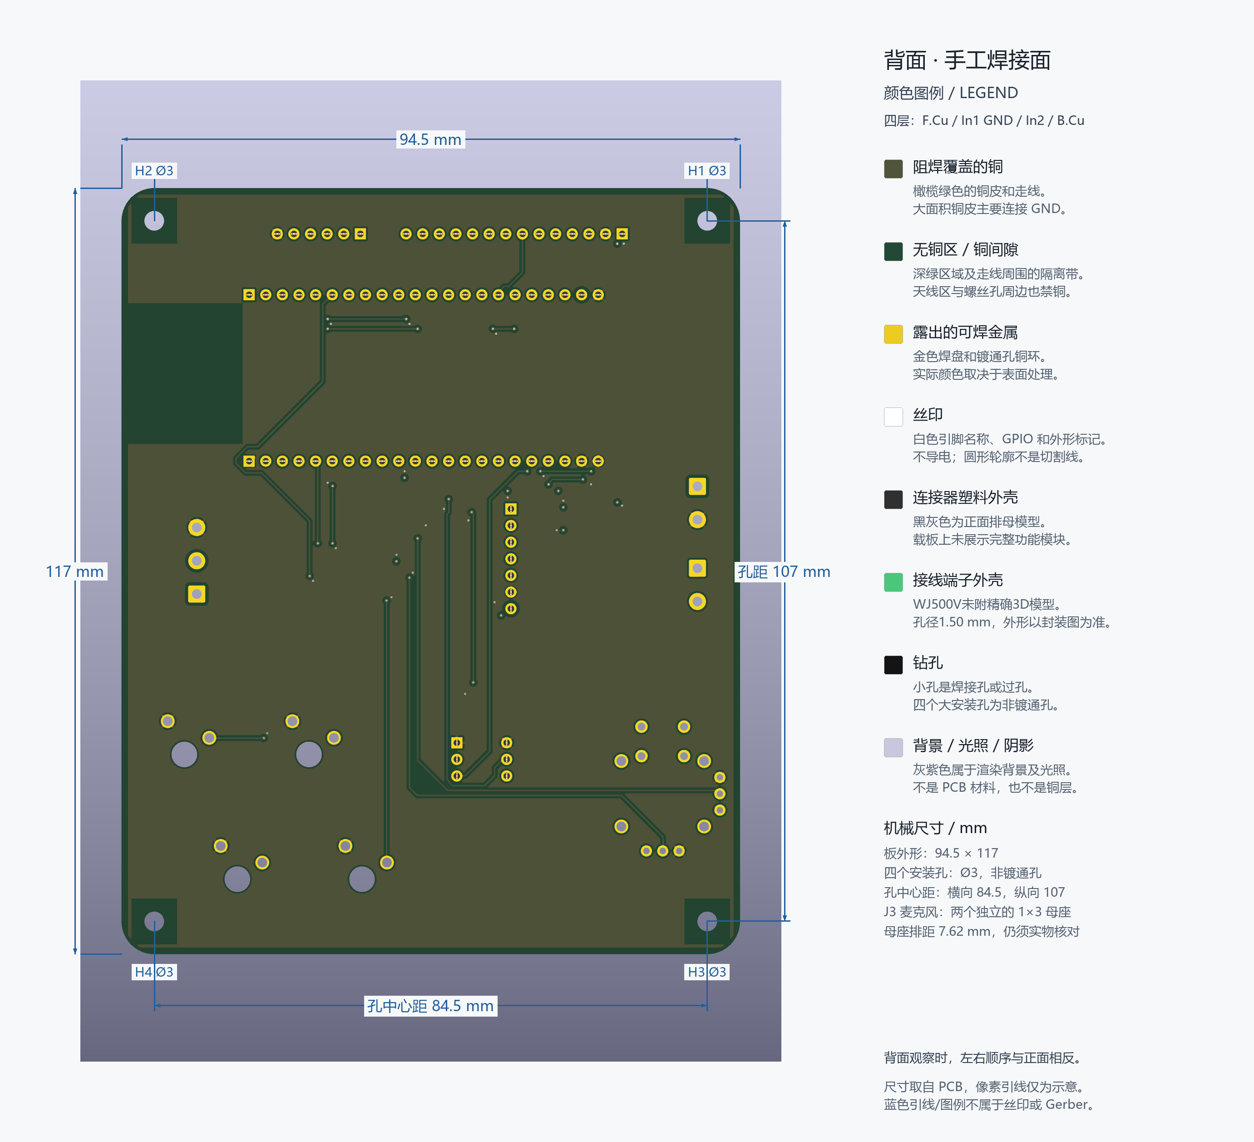
kicad/renders/minibox-carrier-back-legend.png
