richarddzh/minibox/kicad/renders/minibox-carrier-back.png

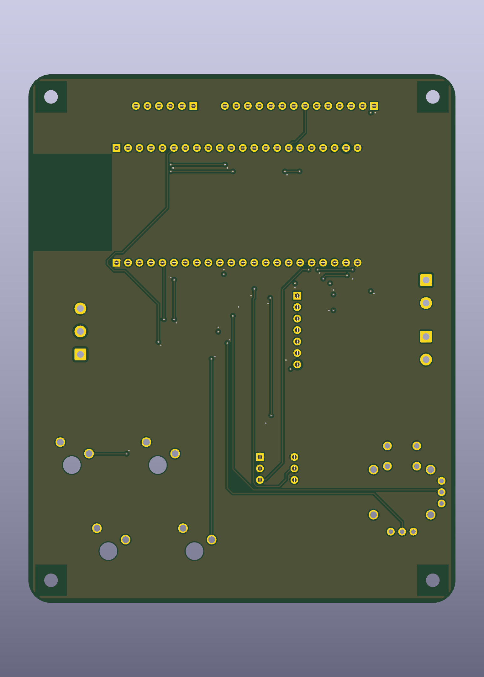
kicad/renders/minibox-carrier-back.png
