richarddzh/minibox/kicad/renders/minibox-carrier-front-legend.png

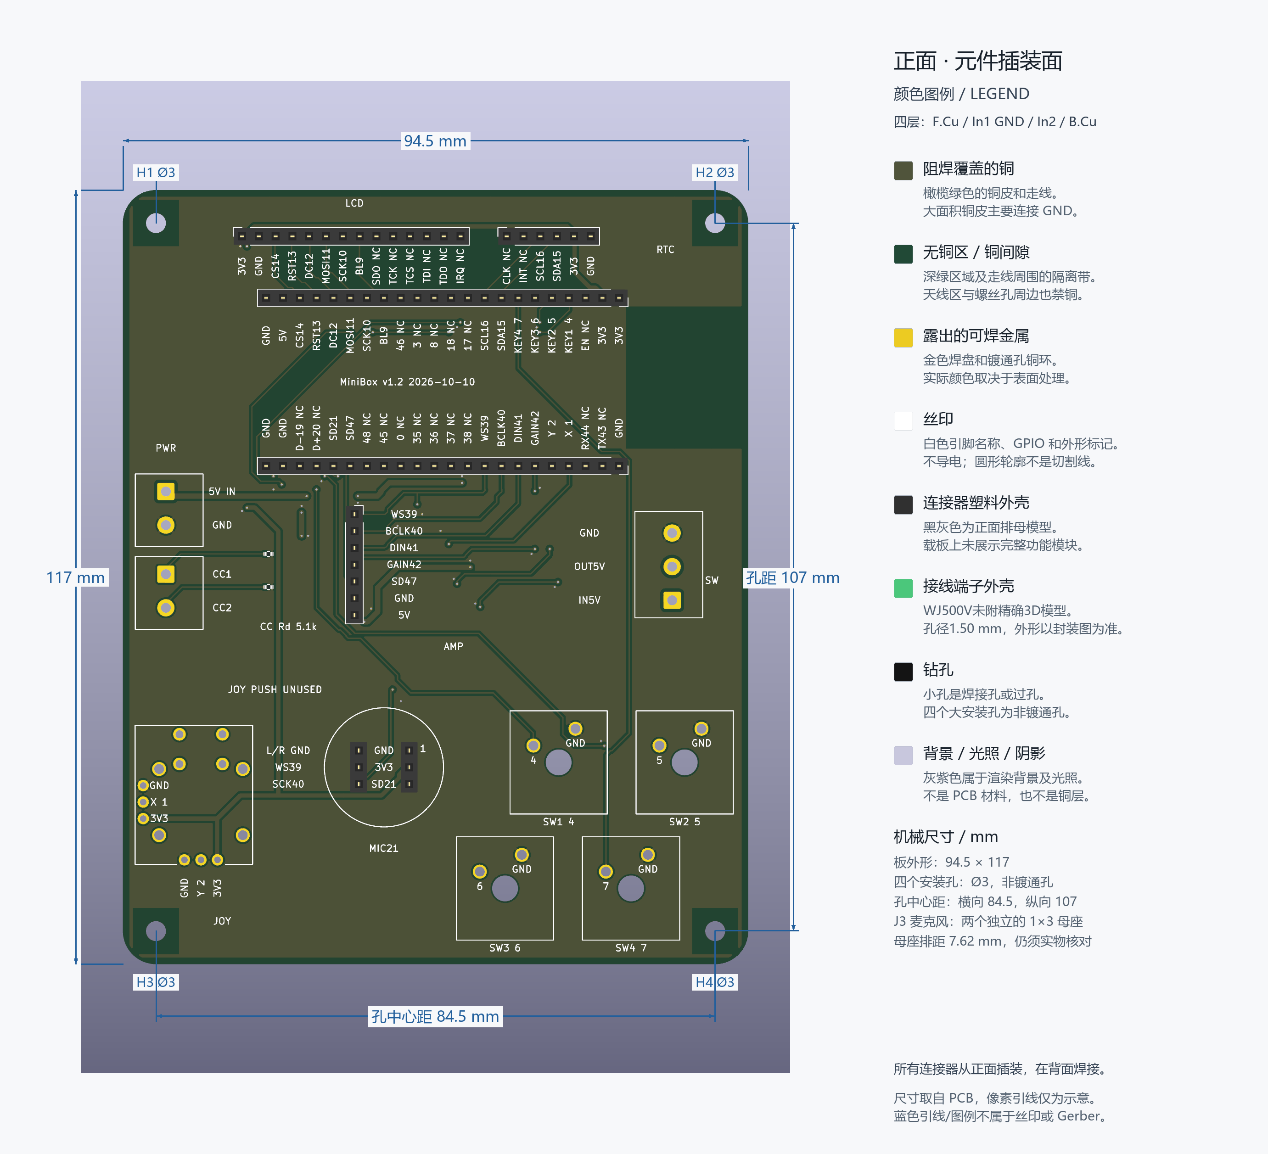
kicad/renders/minibox-carrier-front-legend.png
