richarddzh/minibox/kicad/renders/minibox-carrier-front.png

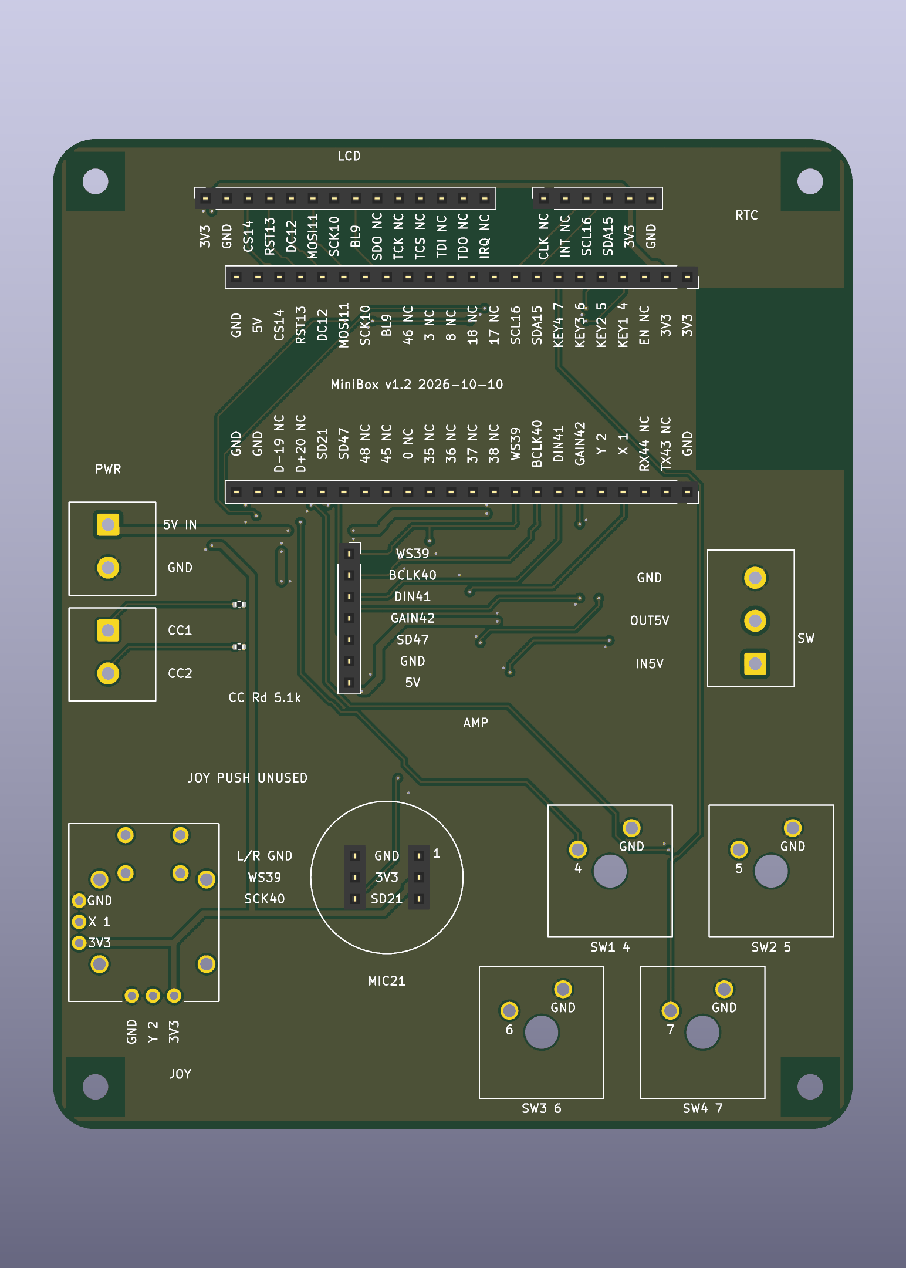
kicad/renders/minibox-carrier-front.png
