richarddzh/minibox/kicad/renders/minibox-carrier-isometric.png

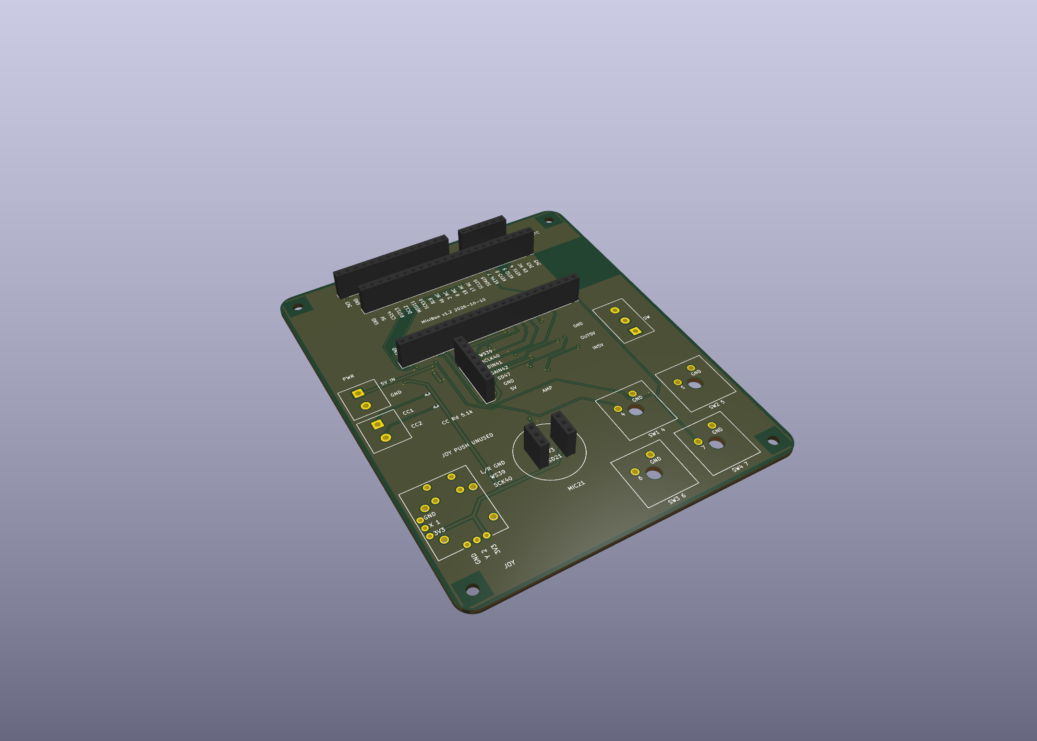
kicad/renders/minibox-carrier-isometric.png
