richarddzh/minibox/models/enclosure-references/control-stack-white.png

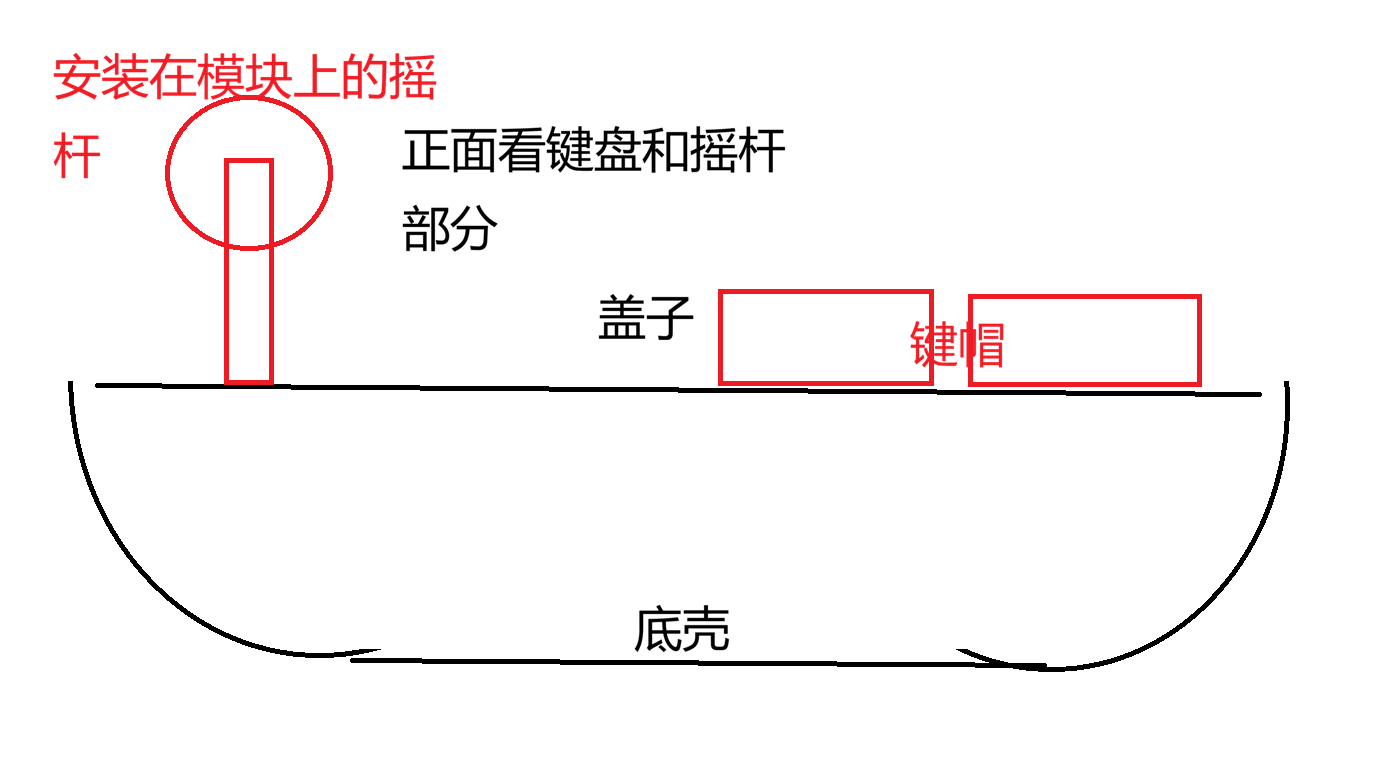
models/enclosure-references/control-stack-white.png
