richarddzh/minibox/models/enclosure-references/controls-layout-white.png

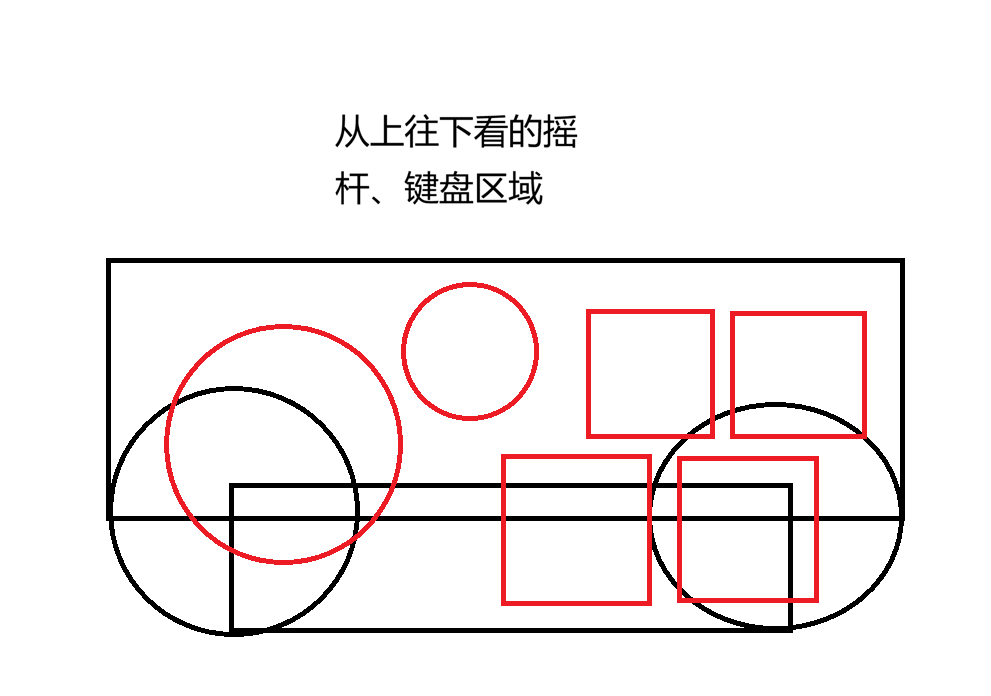
models/enclosure-references/controls-layout-white.png
