richarddzh/minibox/models/enclosure-references/cover-extent-reference.png

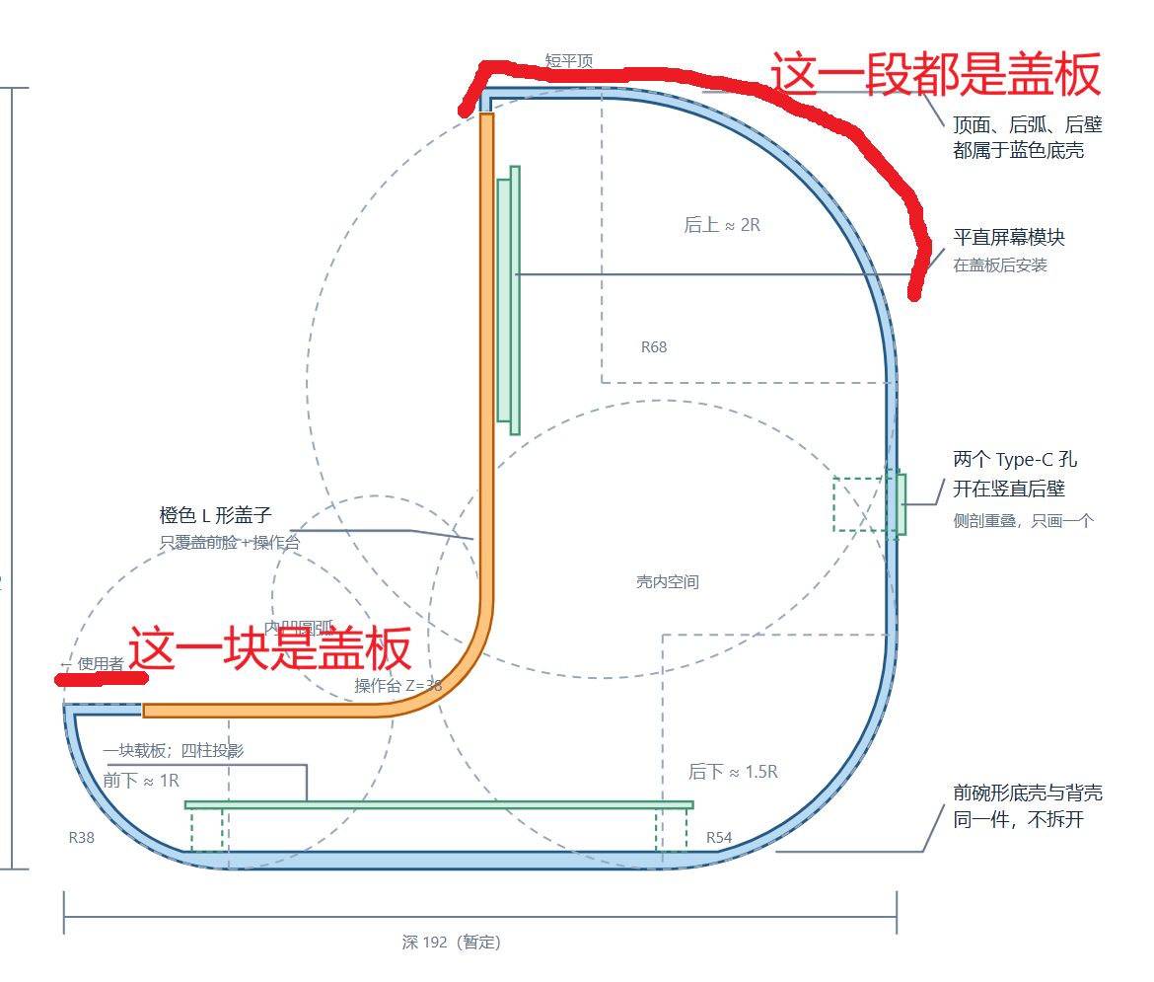
models/enclosure-references/cover-extent-reference.png
