richarddzh/minibox/models/enclosure-references/screen-plan-white.png

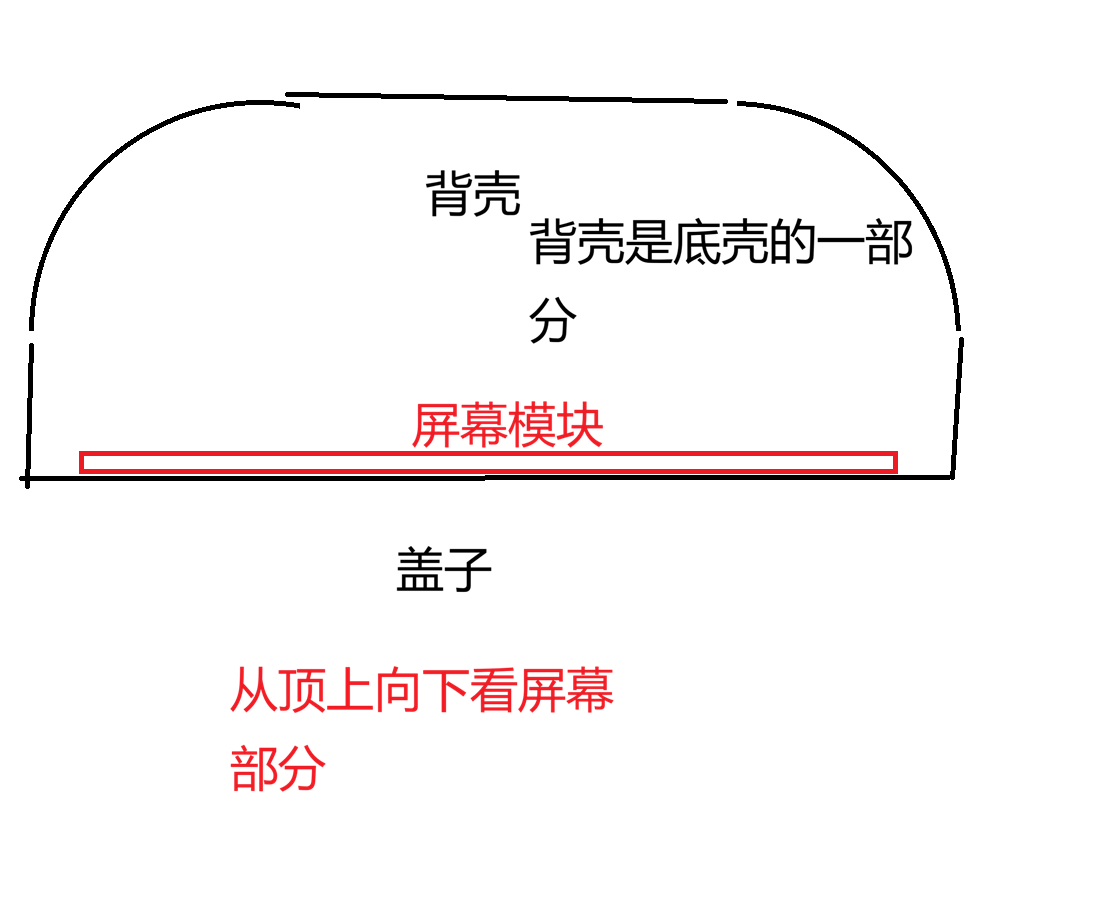
models/enclosure-references/screen-plan-white.png
