richarddzh/minibox/models/enclosure-references/front-construction-white.png

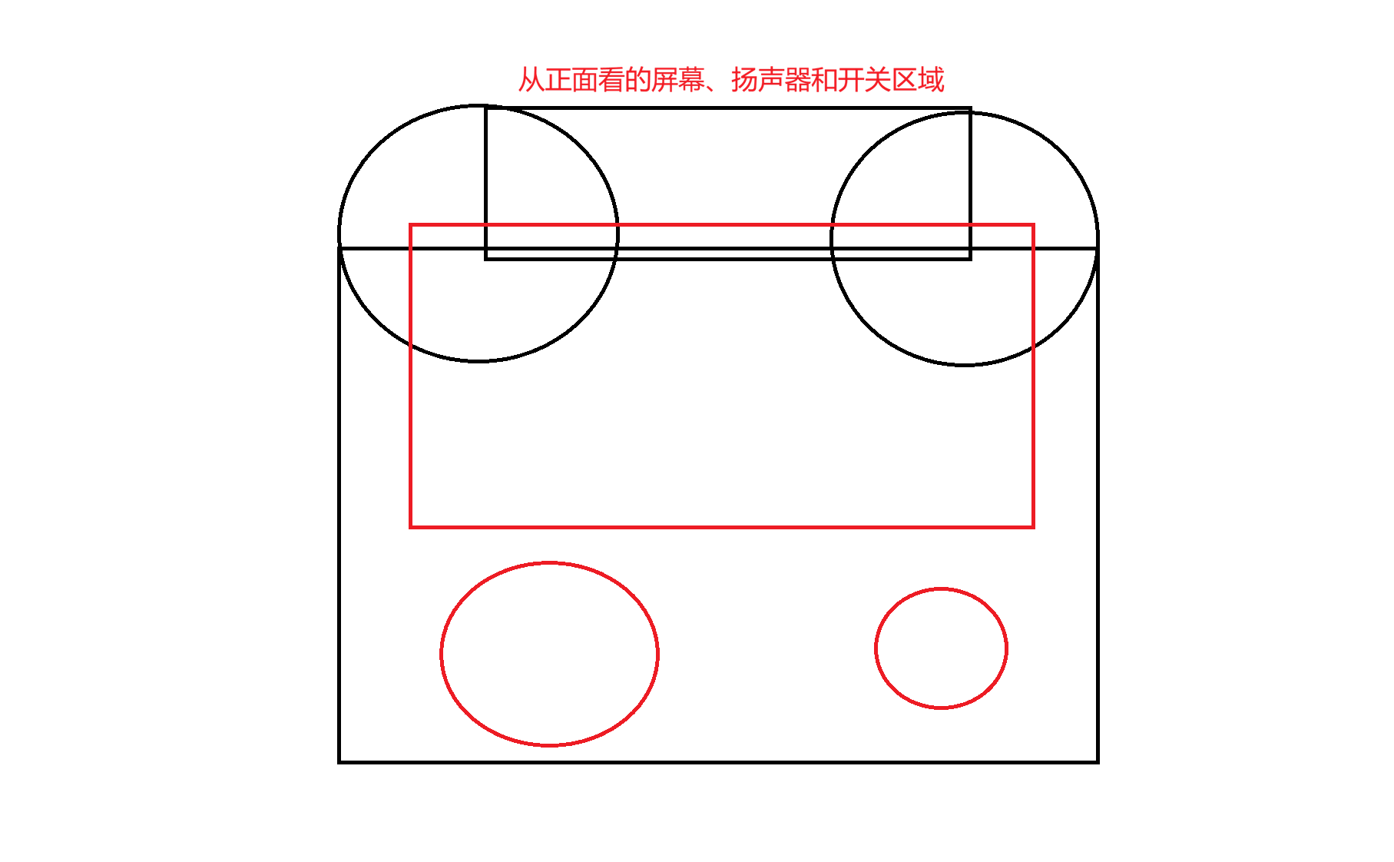
models/enclosure-references/front-construction-white.png
