richarddzh/minibox/models/enclosure-references/side-construction-white.png

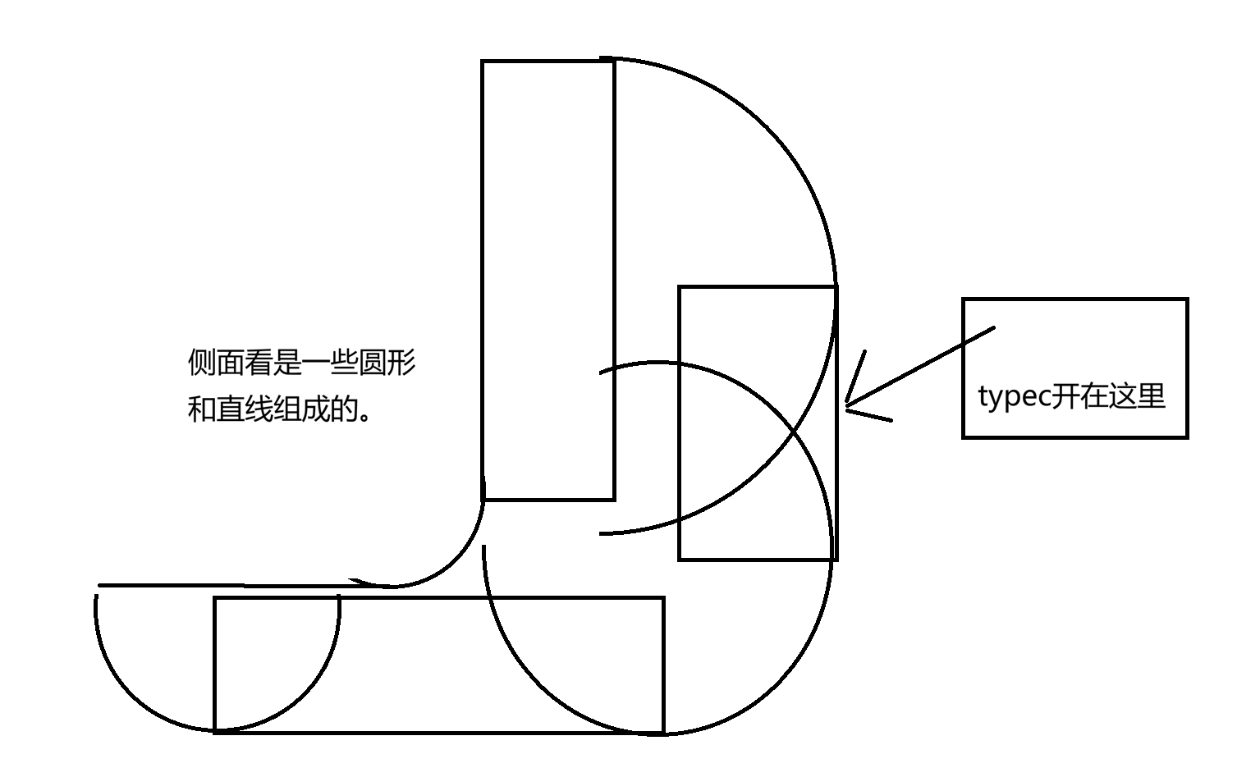
models/enclosure-references/side-construction-white.png
